Vedatori/PaLampa/Manuals/SupportFiles/IMG_4655.jpeg

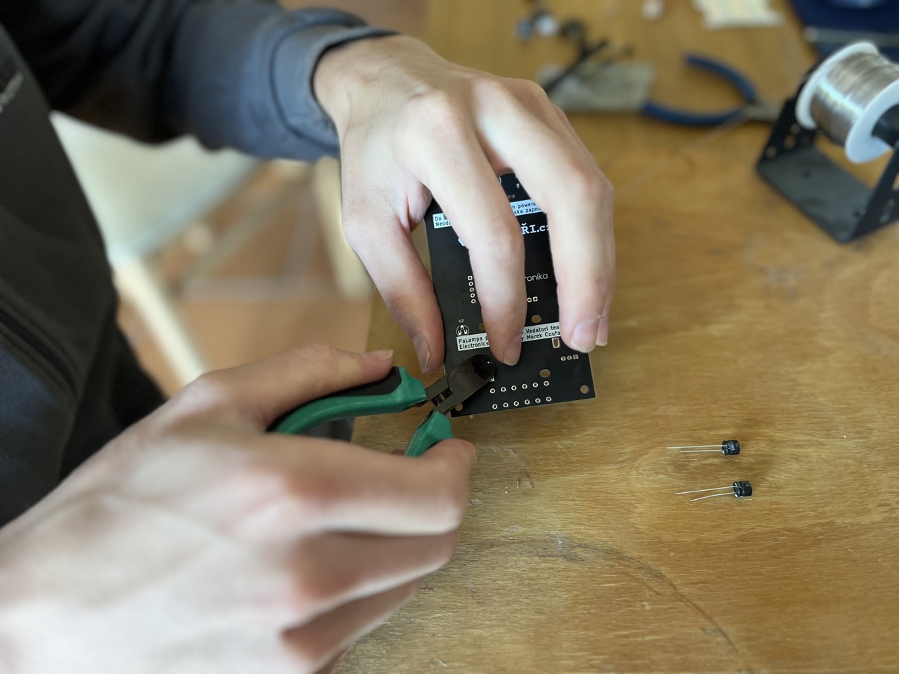
Manuals/SupportFiles/IMG_4655.jpeg
