Vedatori/PaLampa/Manuals/SupportFiles/IMG_4656.jpeg

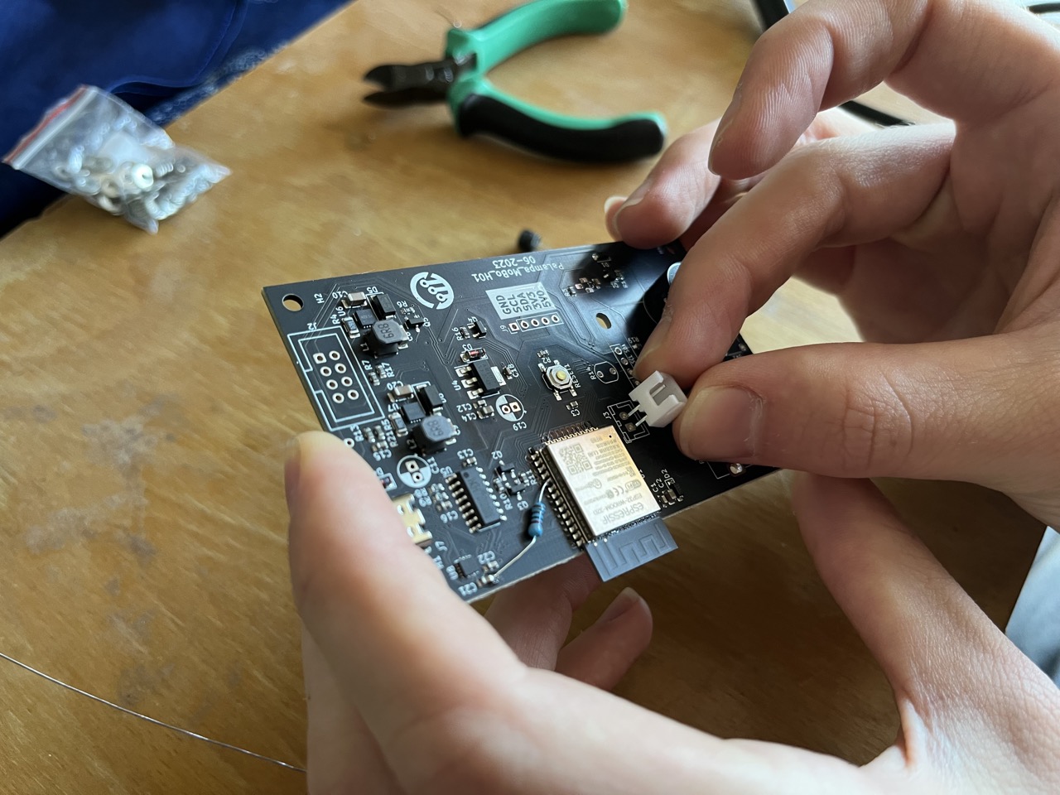
Manuals/SupportFiles/IMG_4656.jpeg
