Vedatori/PaLampa/Manuals/SupportFiles/IMG_4730.jpeg

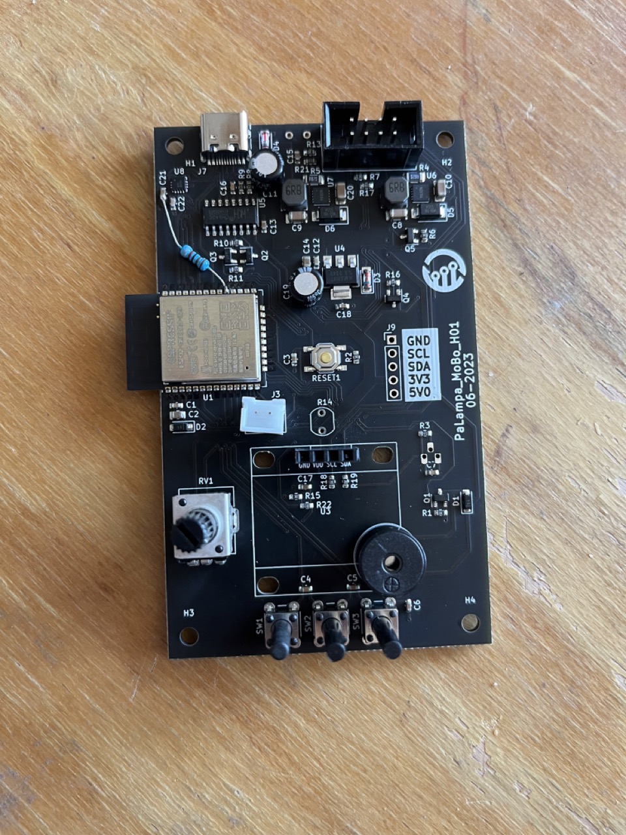
Manuals/SupportFiles/IMG_4730.jpeg
