Vedatori/PaLampa/Manuals/SupportFiles/IMG_5051.jpeg

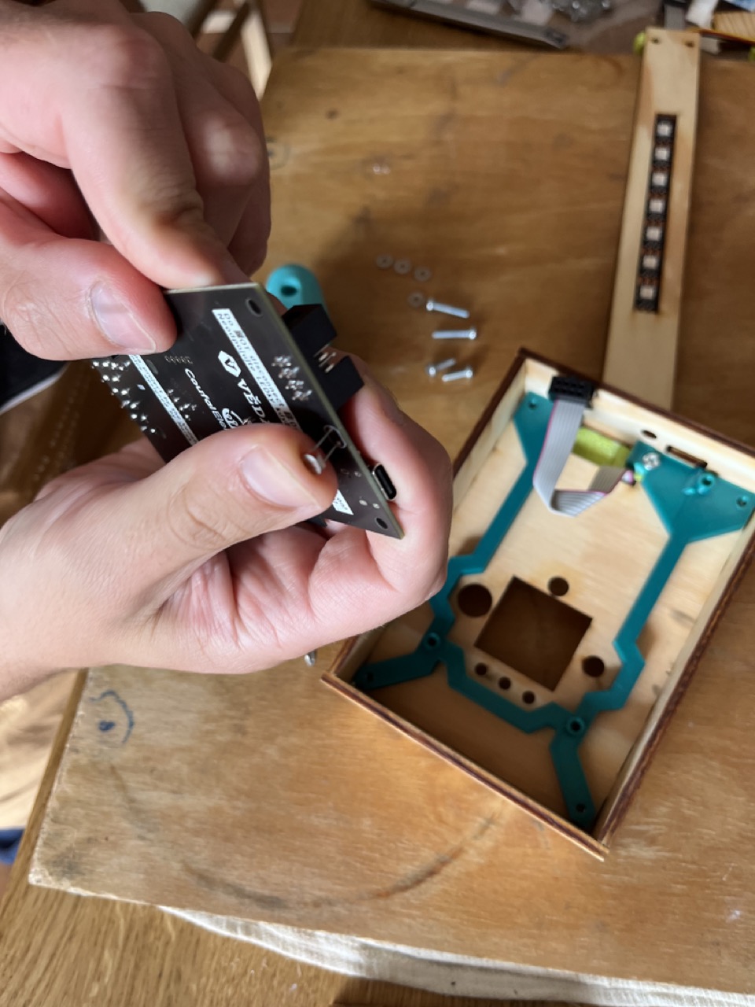
Manuals/SupportFiles/IMG_5051.jpeg
