Vedatori/PaLampa/Manuals/SupportFiles/IMG_5058.jpeg

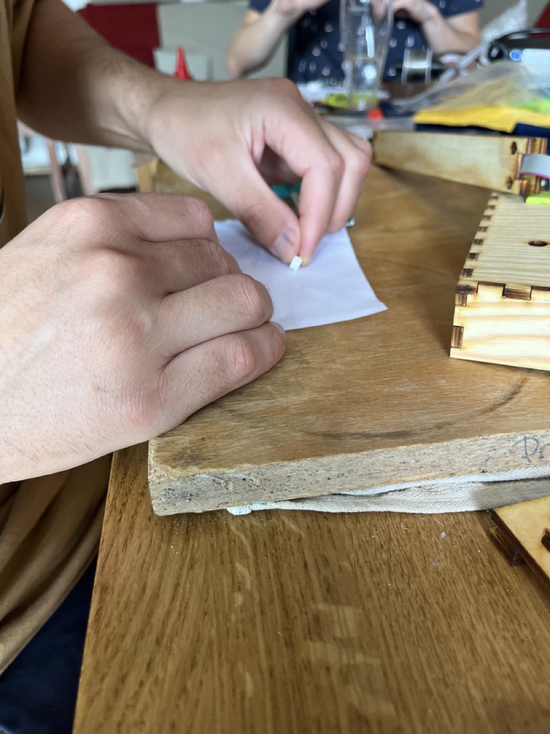
Manuals/SupportFiles/IMG_5058.jpeg
