Vedatori/PaLampa/Manuals/SupportFiles/IMG_5059.jpeg

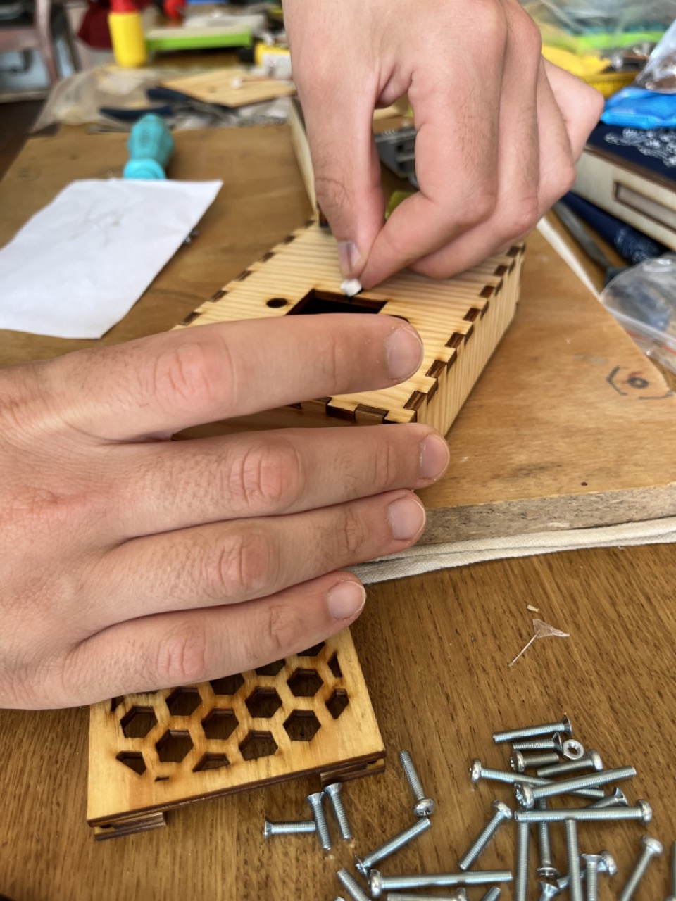
Manuals/SupportFiles/IMG_5059.jpeg
