Vedatori/PaLampa/Manuals/SupportFiles/IMG_5061.jpeg

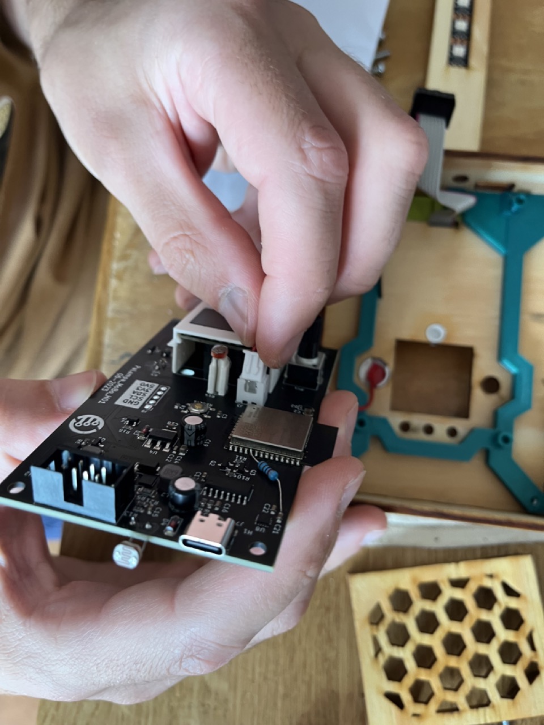
Manuals/SupportFiles/IMG_5061.jpeg
