Vedatori/PaLampa/Manuals/SupportFiles/IMG_5063.jpeg

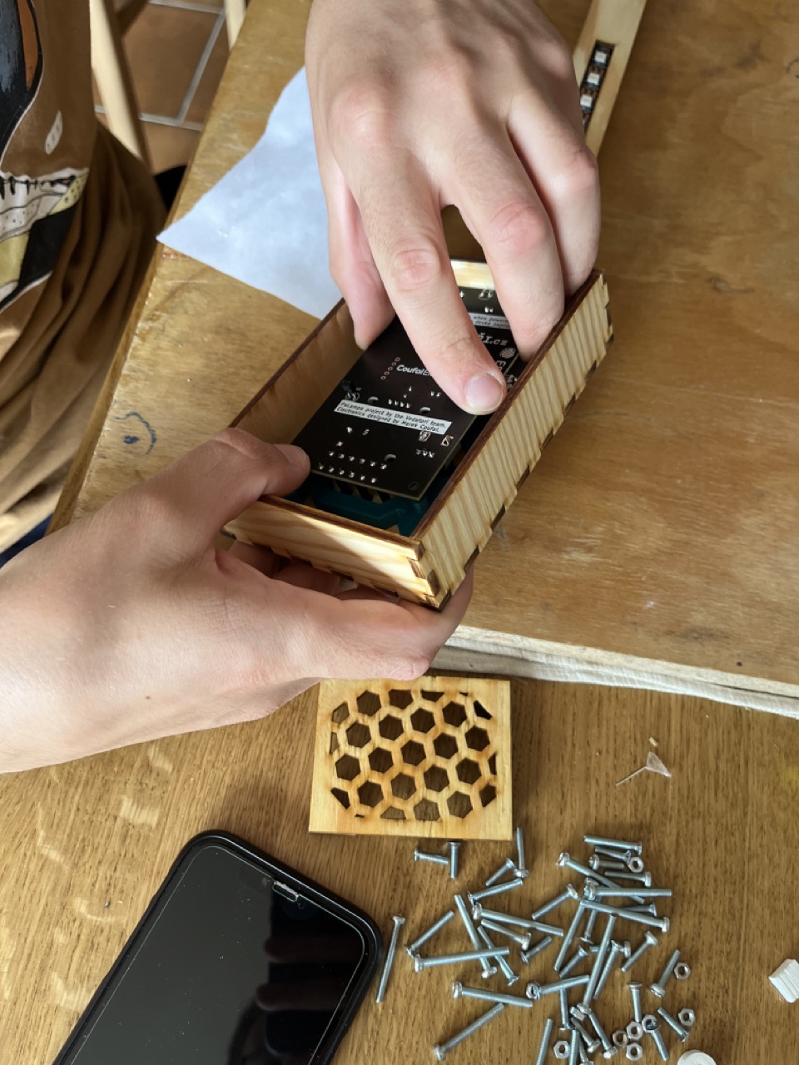
Manuals/SupportFiles/IMG_5063.jpeg
