Vedatori/PaLampa/Manuals/SupportFiles/IMG_5064.jpeg

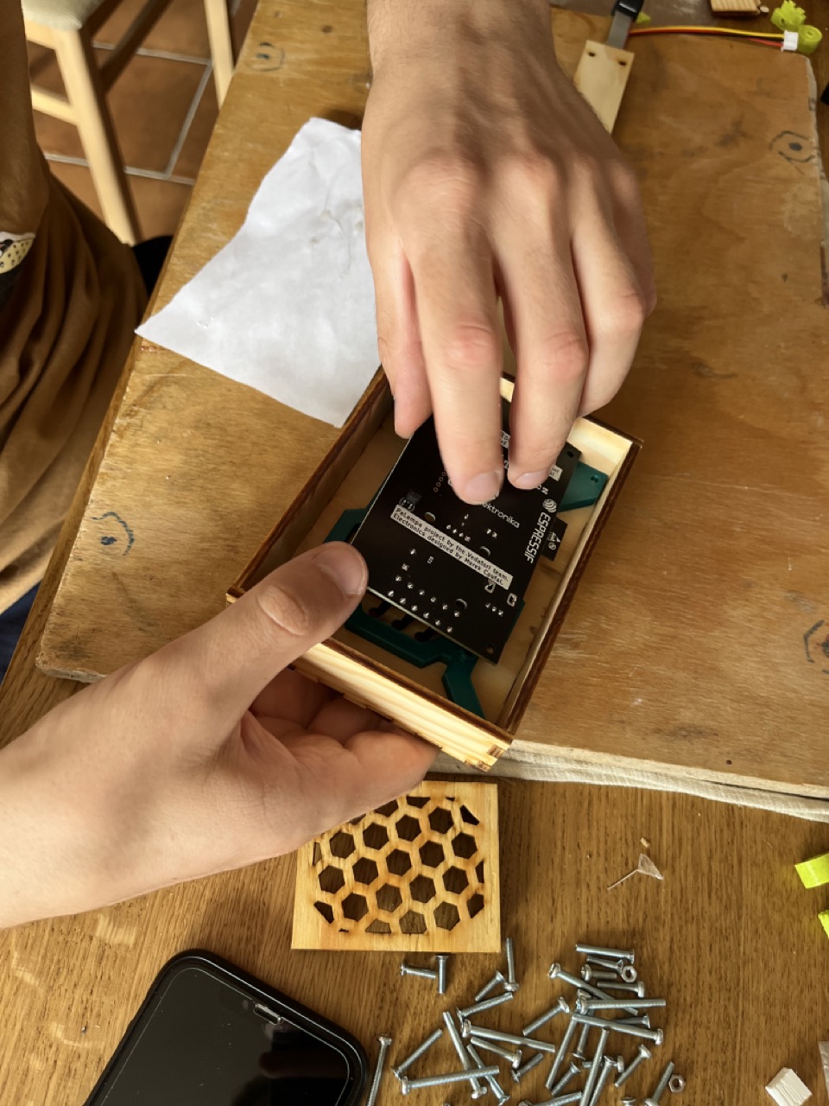
Manuals/SupportFiles/IMG_5064.jpeg
