Vedatori/PaLampa/Manuals/SupportFiles/IMG_5065.jpeg

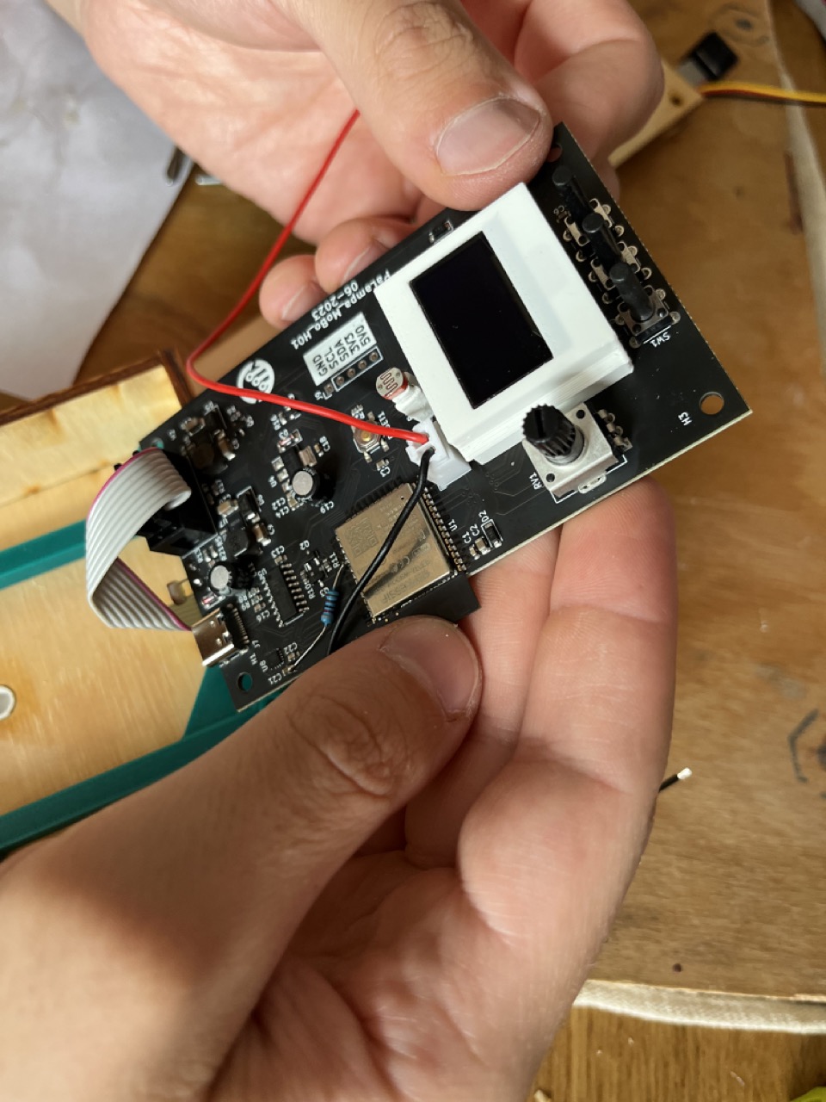
Manuals/SupportFiles/IMG_5065.jpeg
