Vedatori/PaLampa/Manuals/SupportFiles/IMG_5066.jpeg

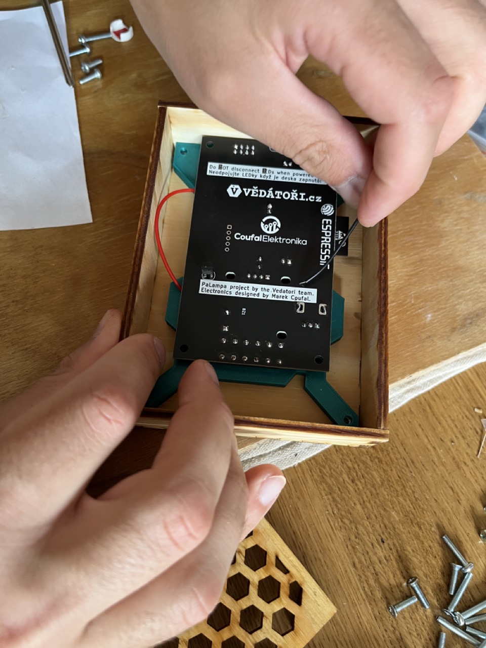
Manuals/SupportFiles/IMG_5066.jpeg
