Vedatori/PaLampa/Manuals/SupportFiles/IMG_5067.jpeg

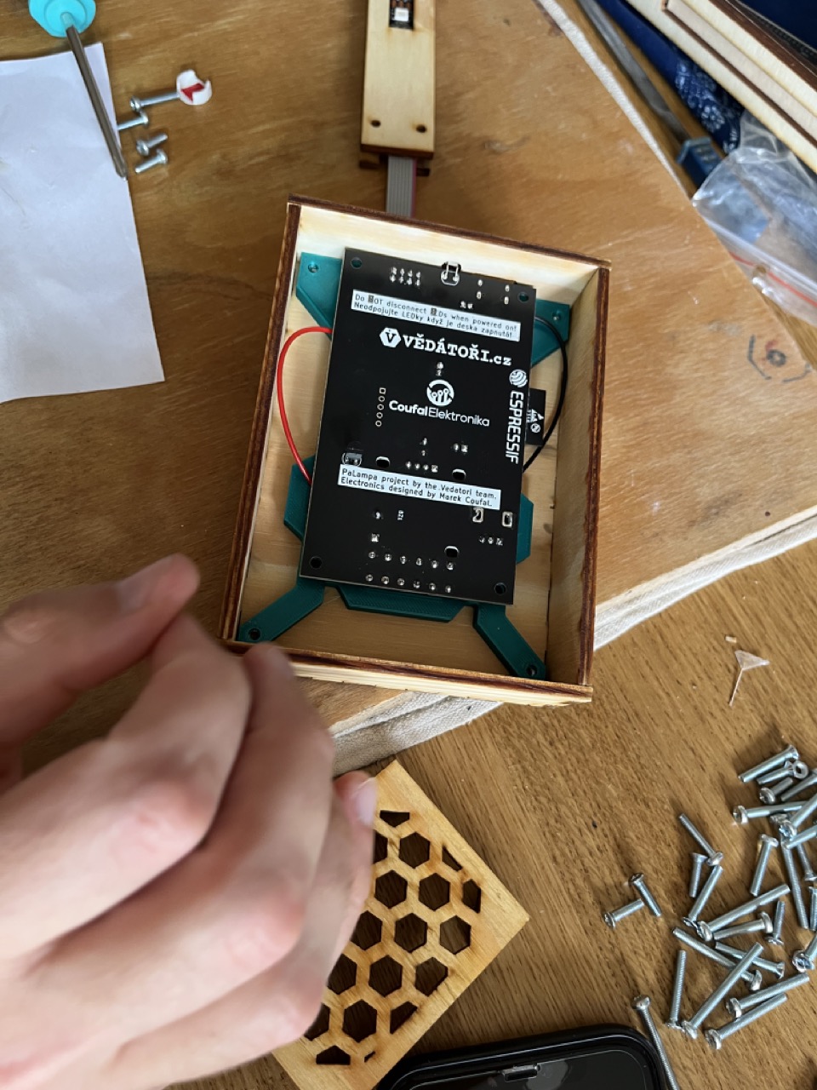
Manuals/SupportFiles/IMG_5067.jpeg
