Vedatori/PaLampa/Manuals/SupportFiles/IMG_5068.jpeg

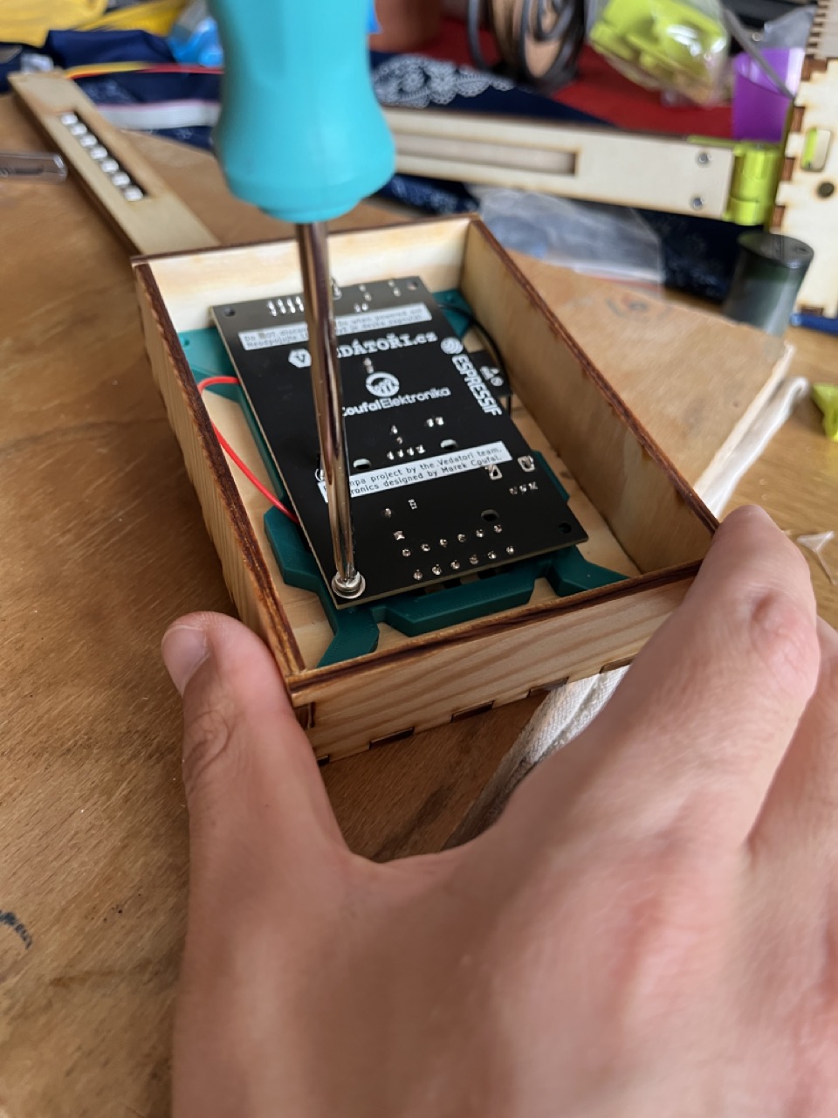
Manuals/SupportFiles/IMG_5068.jpeg
