Vedatori/PaLampa/Manuals/SupportFiles/IMG_5069.jpeg

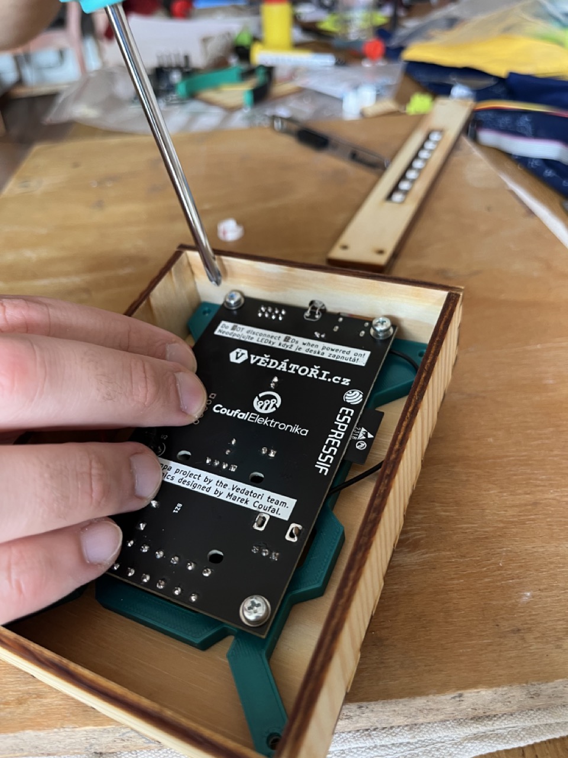
Manuals/SupportFiles/IMG_5069.jpeg
