Vedatori/PaLampa/Manuals/SupportFiles/IMG_5071.jpeg

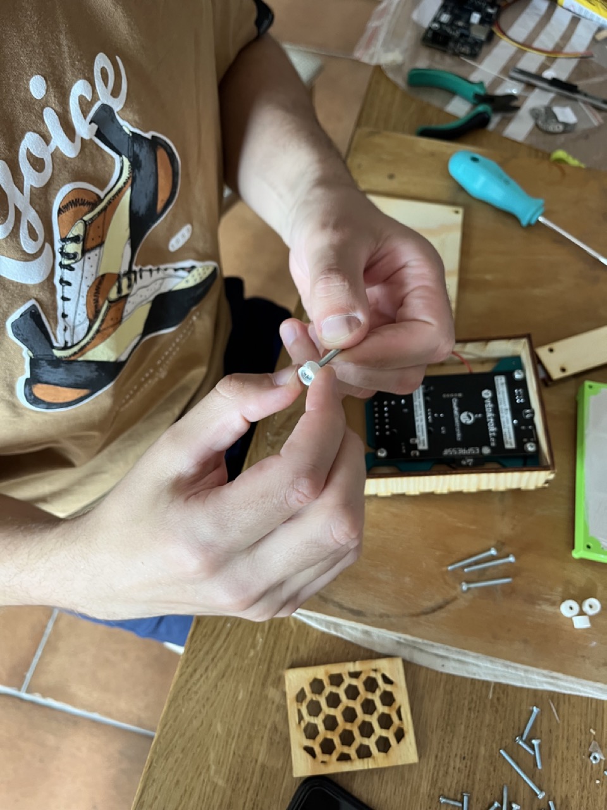
Manuals/SupportFiles/IMG_5071.jpeg
