Vedatori/PaLampa/Manuals/SupportFiles/IMG_5073.jpeg

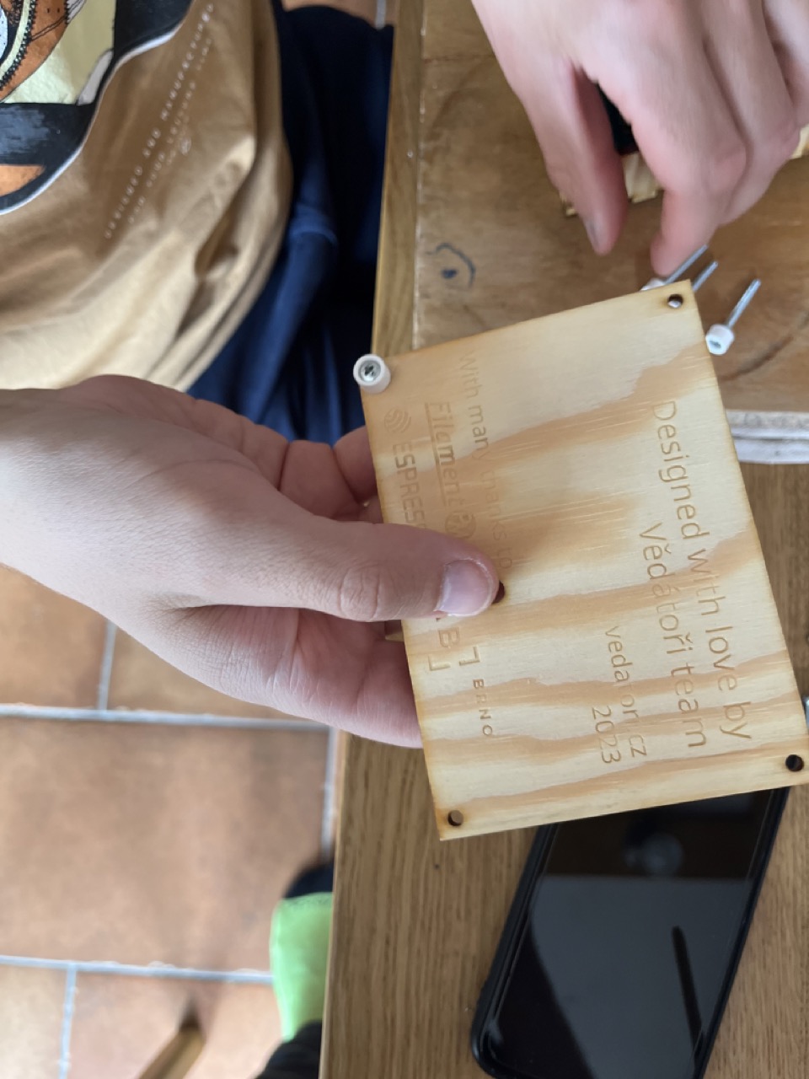
Manuals/SupportFiles/IMG_5073.jpeg
