Vedatori/PaLampa/Manuals/SupportFiles/IMG_5074.jpeg

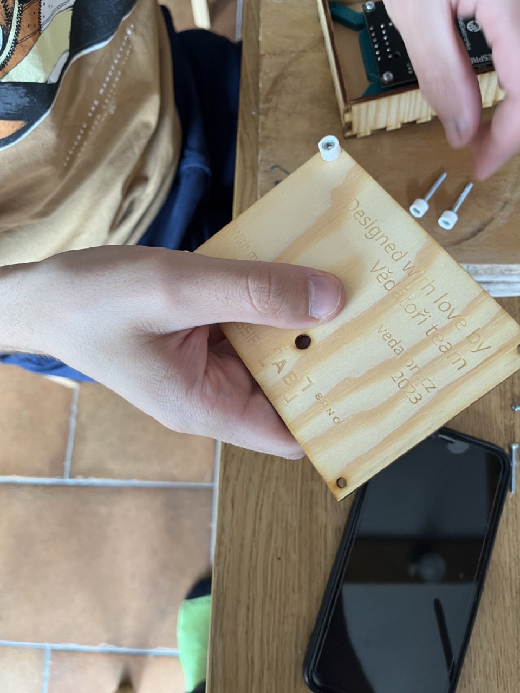
Manuals/SupportFiles/IMG_5074.jpeg
