Vedatori/PaLampa/Manuals/SupportFiles/IMG_5075.jpeg

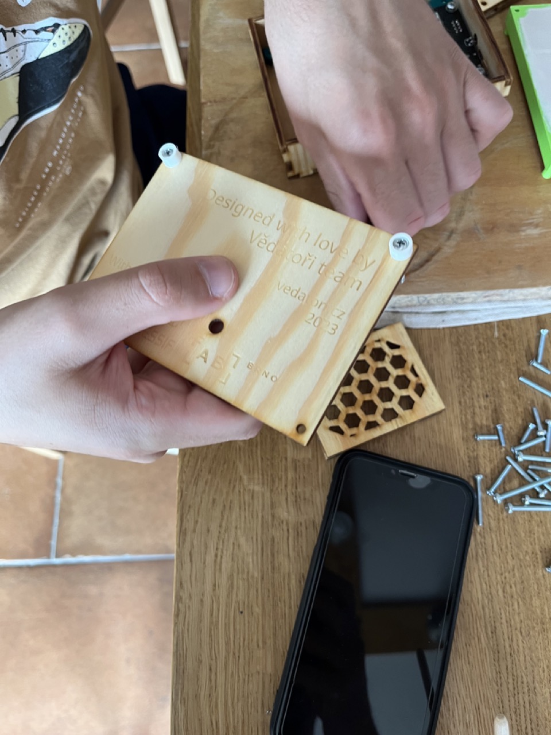
Manuals/SupportFiles/IMG_5075.jpeg
