Vedatori/PaLampa/Manuals/SupportFiles/IMG_5076.jpeg

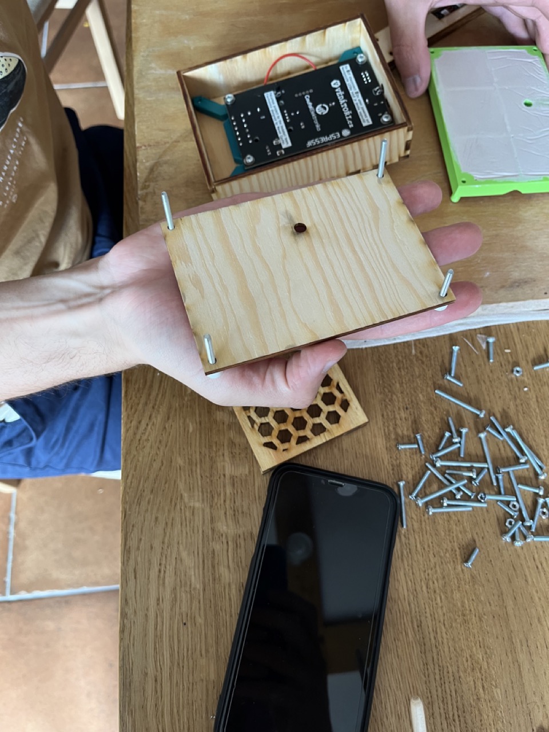
Manuals/SupportFiles/IMG_5076.jpeg
