Vedatori/PaLampa/Manuals/SupportFiles/IMG_5078.jpeg

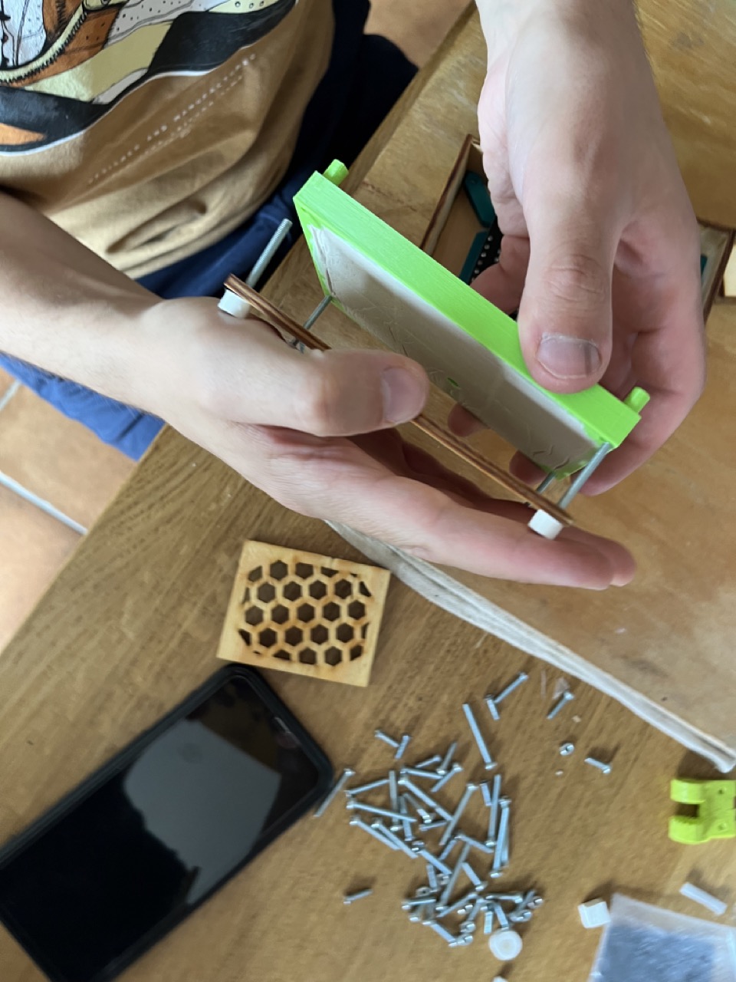
Manuals/SupportFiles/IMG_5078.jpeg
