Vedatori/PaLampa/Manuals/SupportFiles/IMG_5079.jpeg

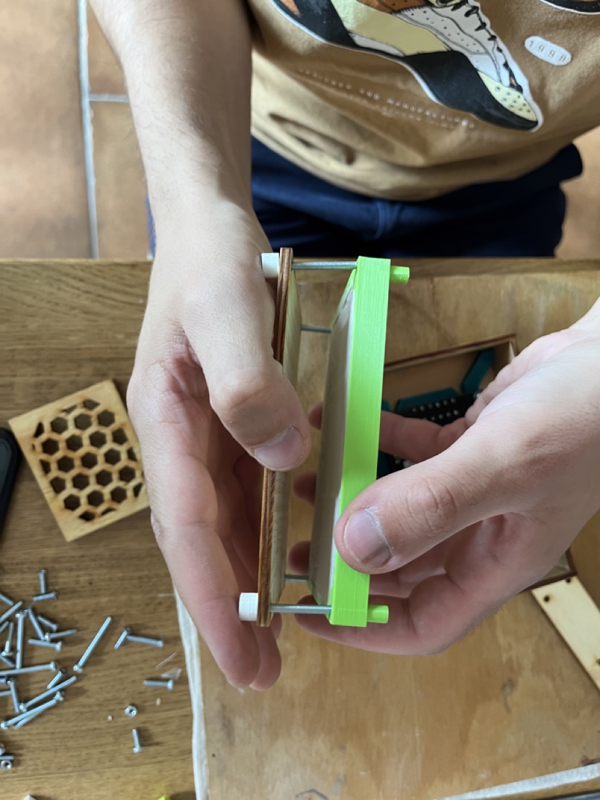
Manuals/SupportFiles/IMG_5079.jpeg
