Vedatori/PaLampa/Manuals/SupportFiles/IMG_5080.jpeg

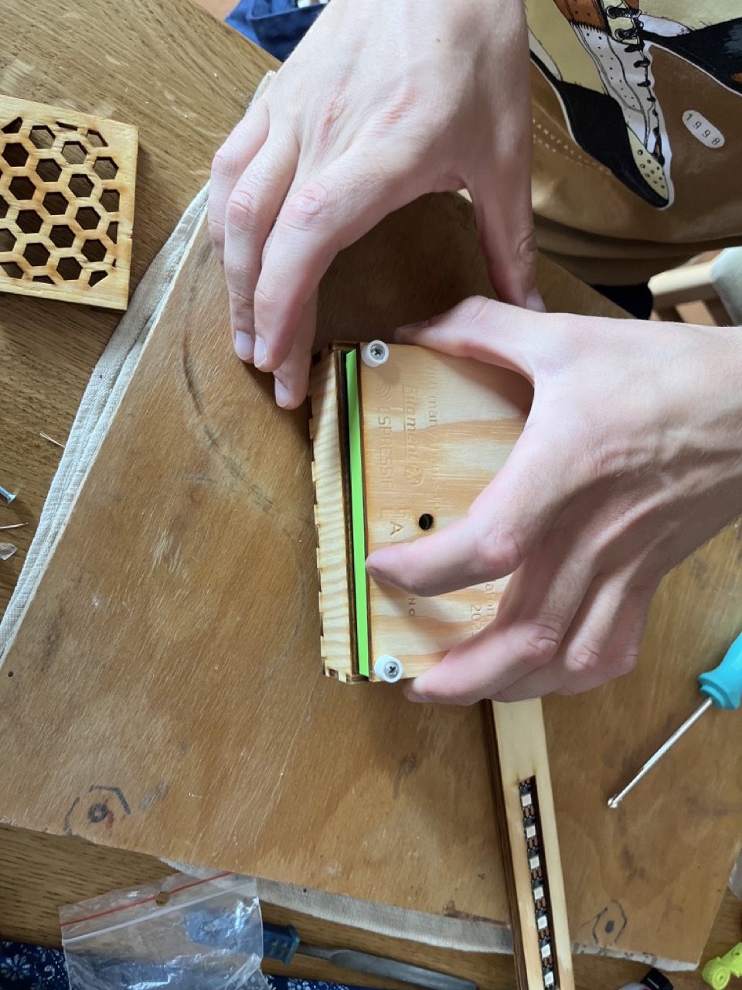
Manuals/SupportFiles/IMG_5080.jpeg
