Vedatori/PaLampa/Manuals/SupportFiles/IMG_5081.jpeg

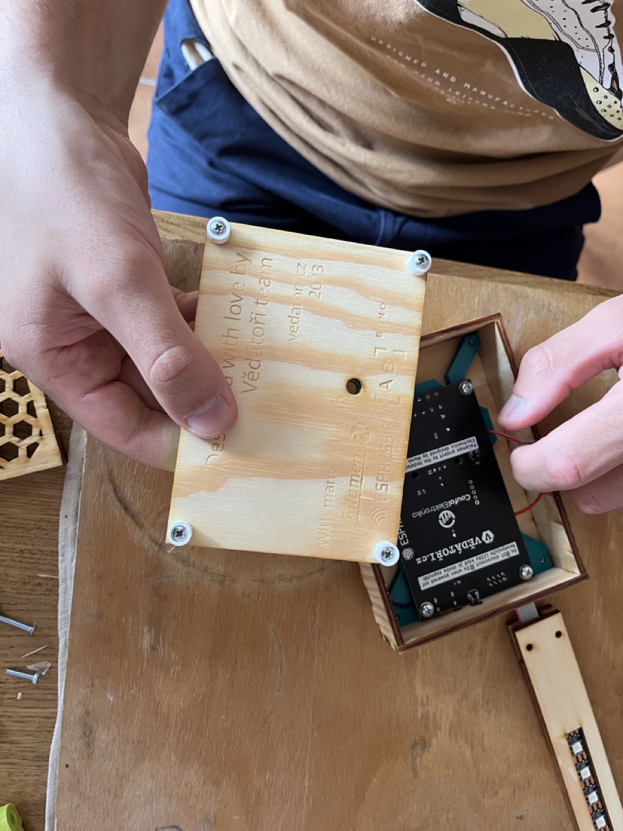
Manuals/SupportFiles/IMG_5081.jpeg
