Vedatori/PaLampa/Manuals/SupportFiles/IMG_5082.jpeg

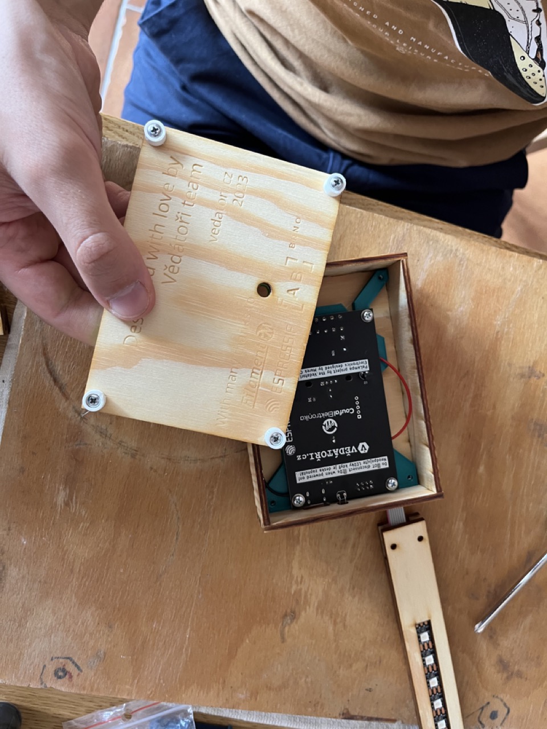
Manuals/SupportFiles/IMG_5082.jpeg
