Vedatori/PaLampa/Manuals/SupportFiles/IMG_5088.jpeg

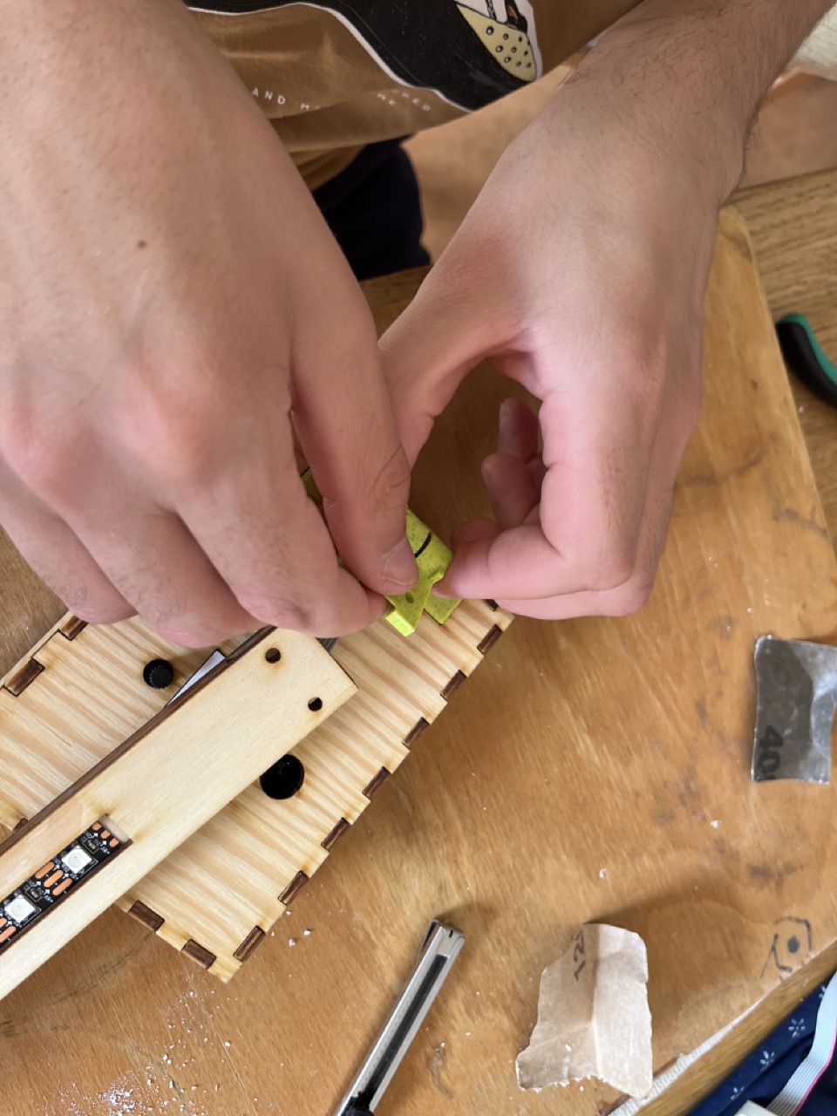
Manuals/SupportFiles/IMG_5088.jpeg
