Vedatori/PaLampa/Manuals/SupportFiles/IMG_5090.jpeg

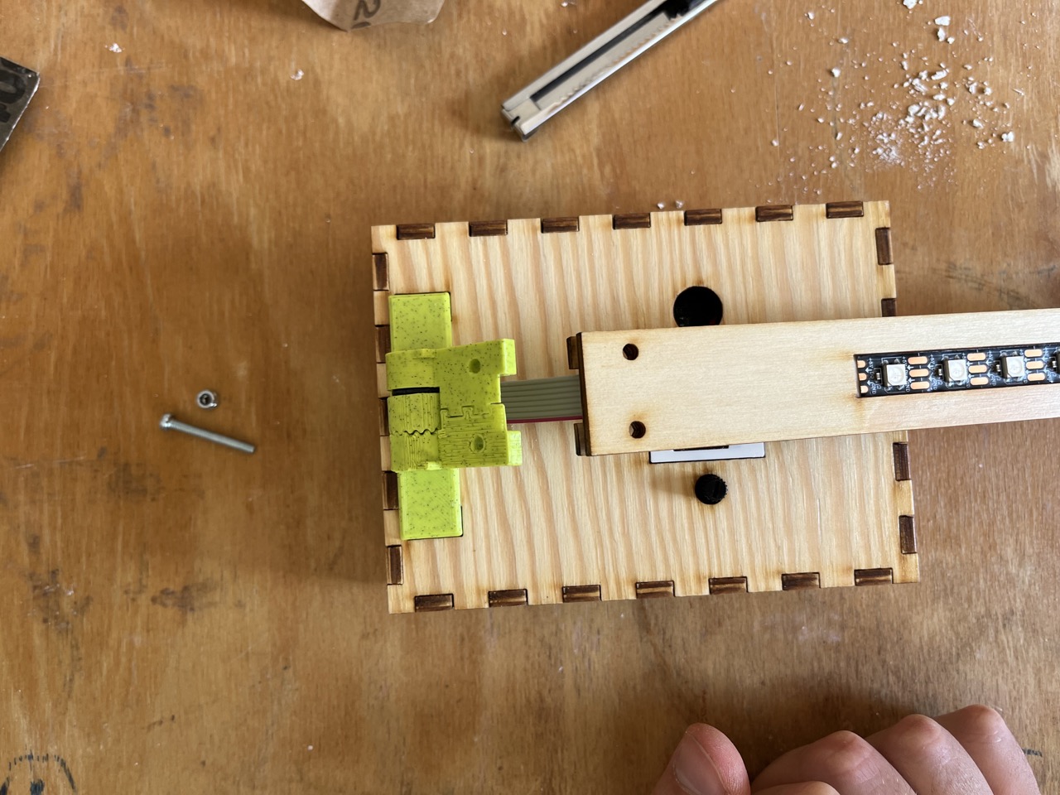
Manuals/SupportFiles/IMG_5090.jpeg
