Vedatori/PaLampa/Manuals/SupportFiles/IMG_5092.jpeg

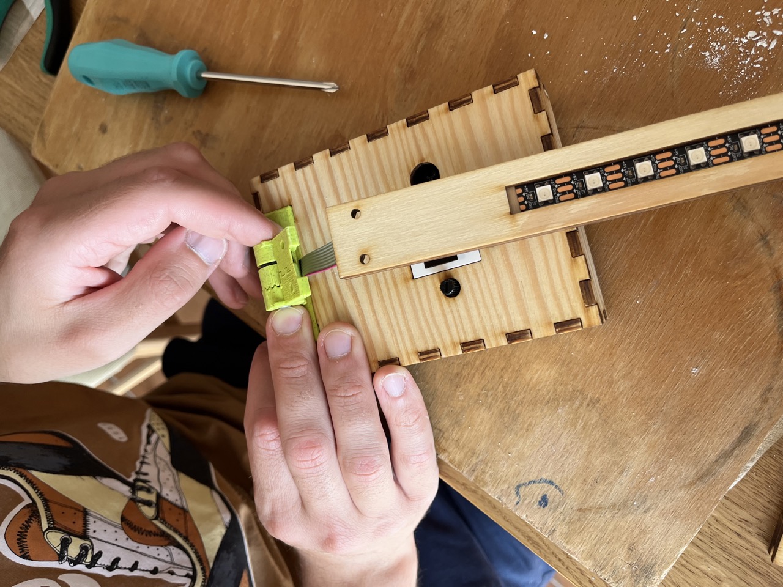
Manuals/SupportFiles/IMG_5092.jpeg
