Vedatori/PaLampa/Manuals/SupportFiles/IMG_5093.jpeg

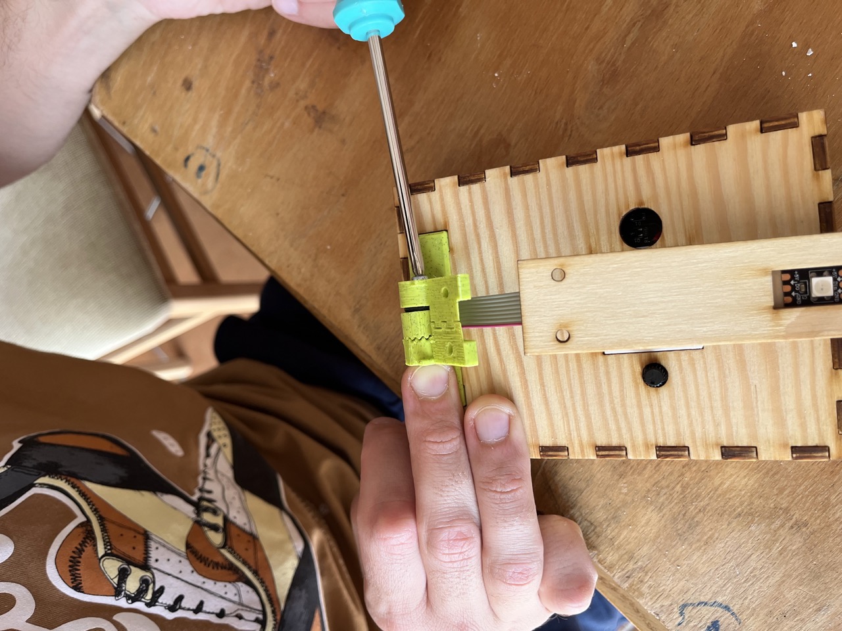
Manuals/SupportFiles/IMG_5093.jpeg
