Vedatori/PaLampa/Manuals/SupportFiles/IMG_5094.jpeg

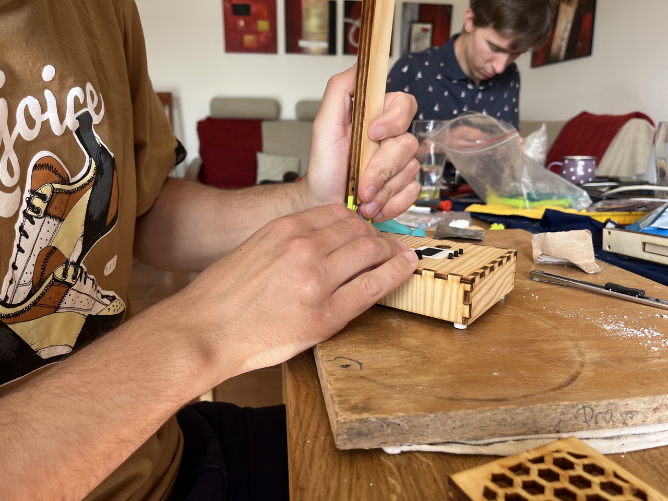
Manuals/SupportFiles/IMG_5094.jpeg
