Vedatori/PaLampa/Manuals/SupportFiles/IMG_5096.jpeg

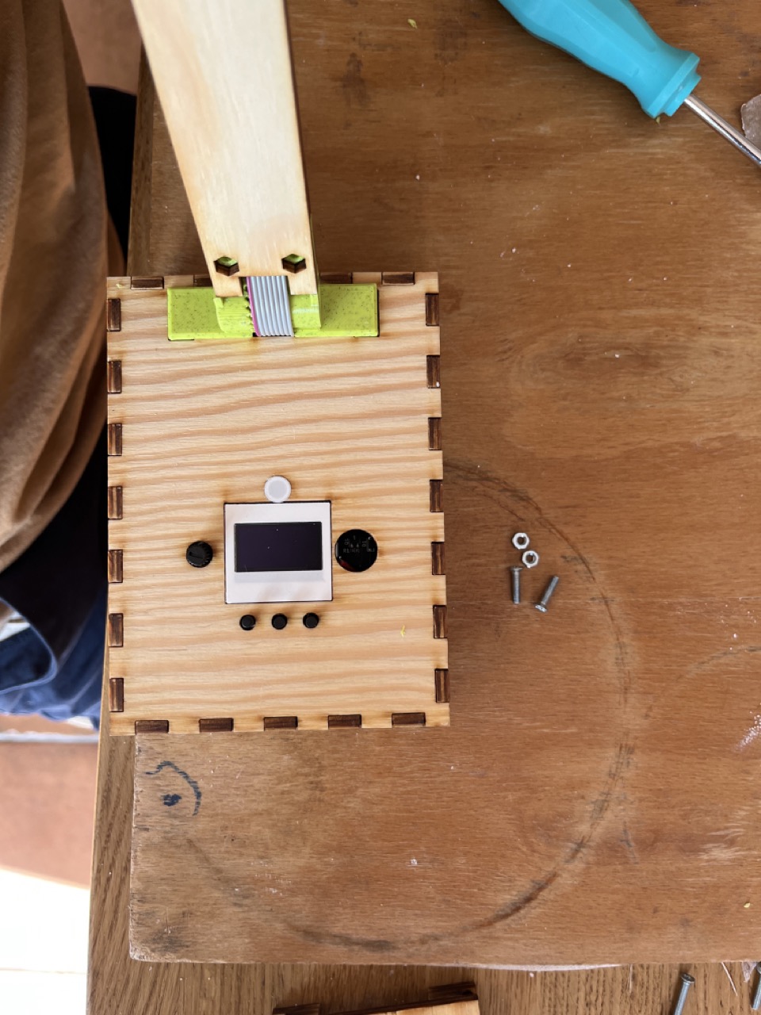
Manuals/SupportFiles/IMG_5096.jpeg
