Vedatori/PaLampa/Manuals/SupportFiles/IMG_5098.jpeg

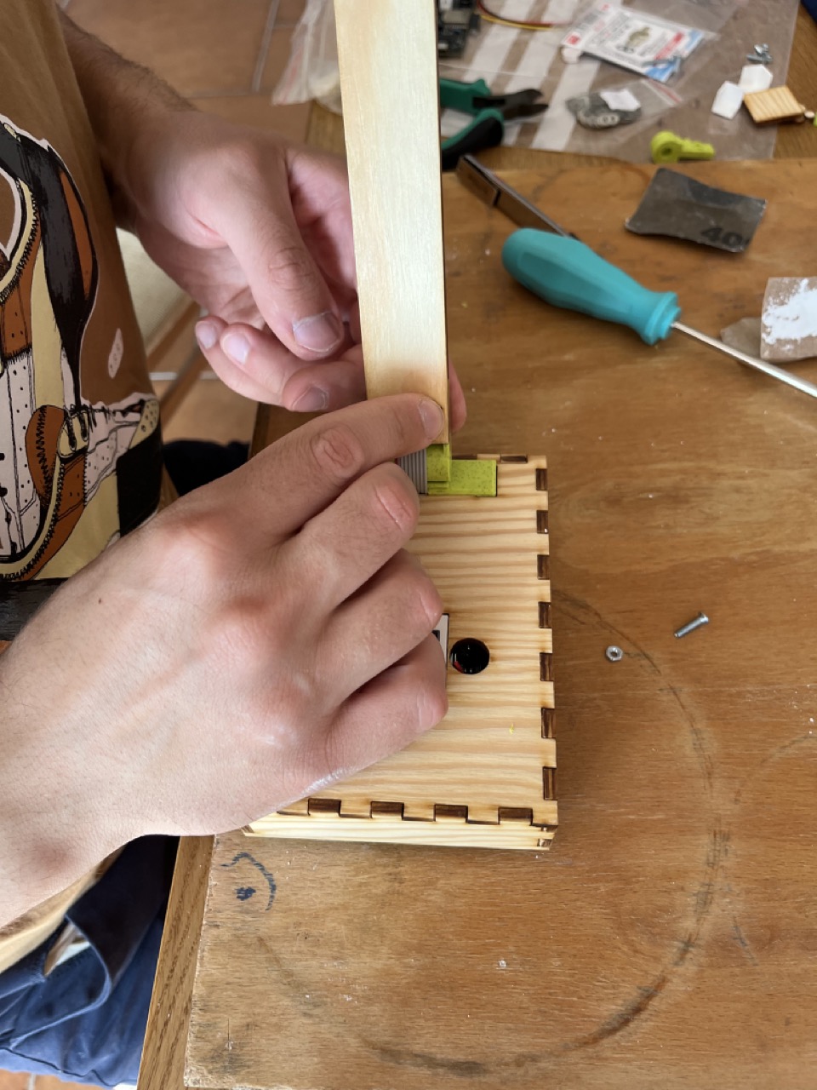
Manuals/SupportFiles/IMG_5098.jpeg
