Vedatori/PaLampa/Manuals/SupportFiles/IMG_5101.jpeg

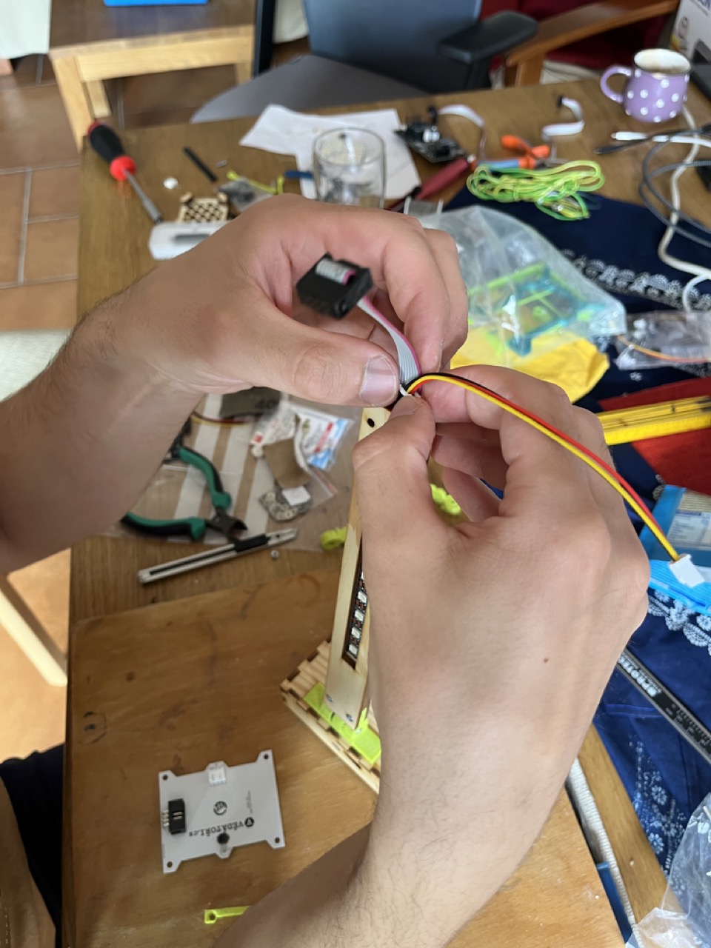
Manuals/SupportFiles/IMG_5101.jpeg
