Vedatori/PaLampa/Manuals/SupportFiles/IMG_5102.jpeg

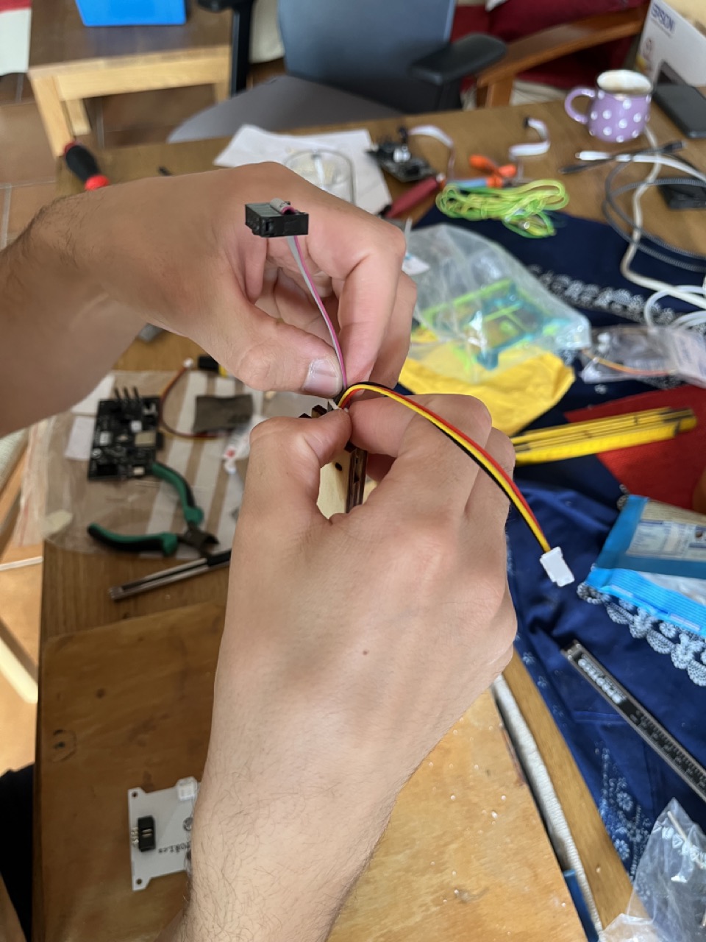
Manuals/SupportFiles/IMG_5102.jpeg
