Vedatori/PaLampa/Manuals/SupportFiles/IMG_5104.jpeg

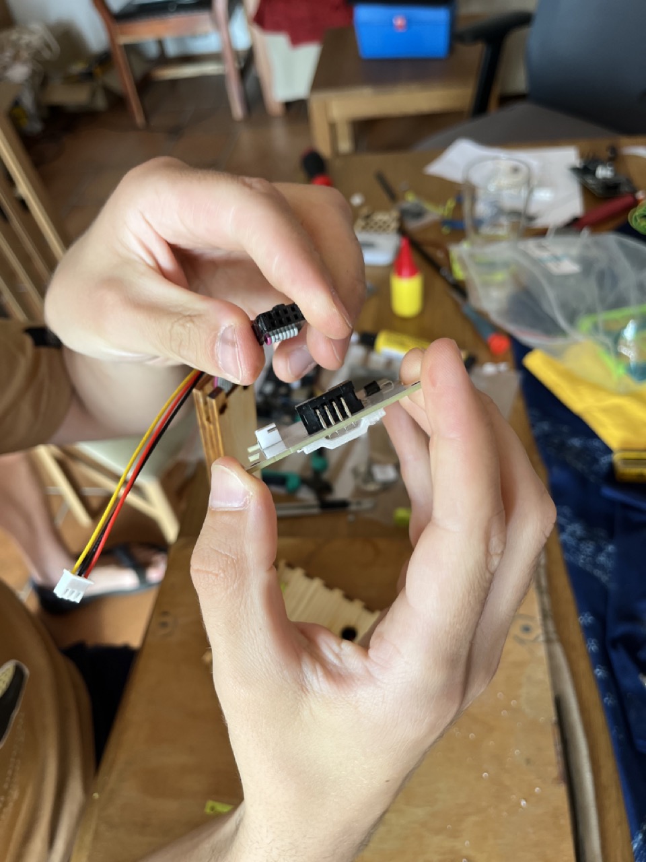
Manuals/SupportFiles/IMG_5104.jpeg
