Vedatori/PaLampa/Manuals/SupportFiles/IMG_5105.jpeg

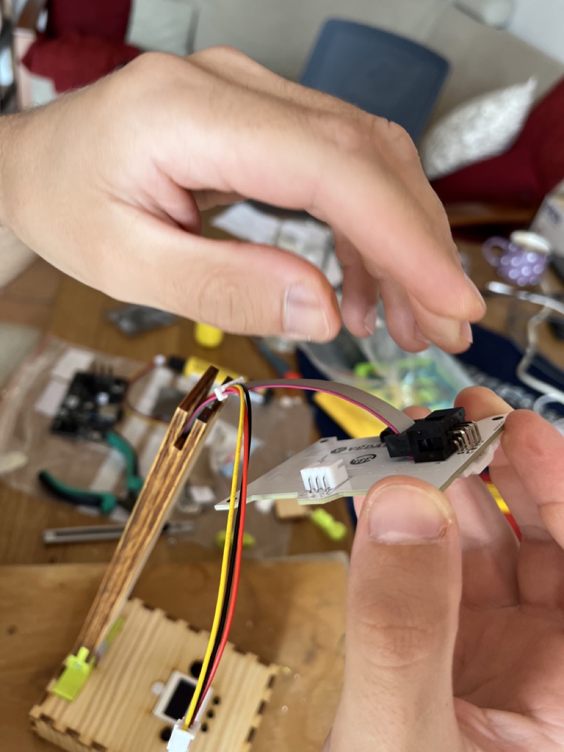
Manuals/SupportFiles/IMG_5105.jpeg
