Vedatori/PaLampa/Manuals/SupportFiles/IMG_5106.jpeg

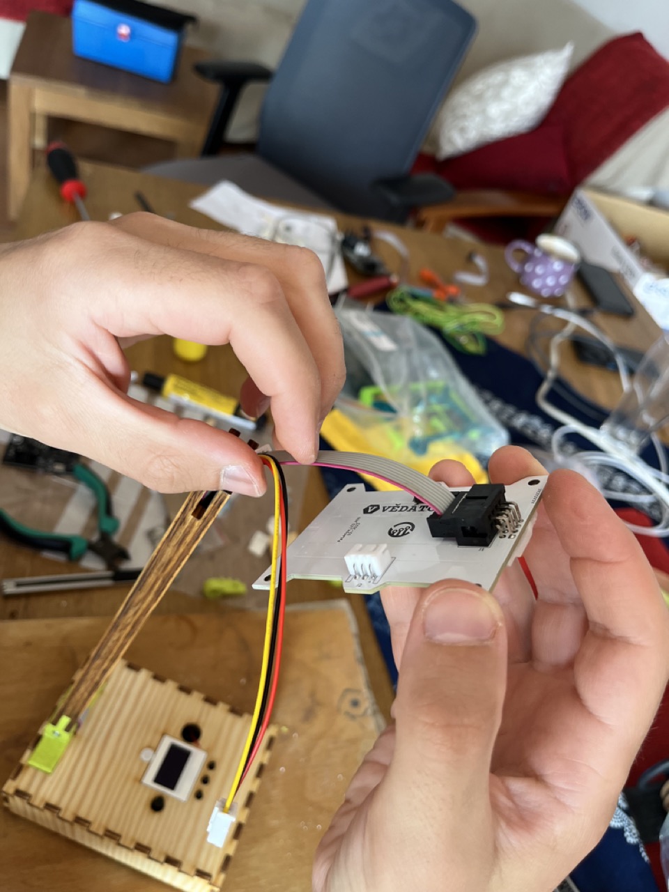
Manuals/SupportFiles/IMG_5106.jpeg
