Vedatori/PaLampa/Manuals/SupportFiles/IMG_5108.jpeg

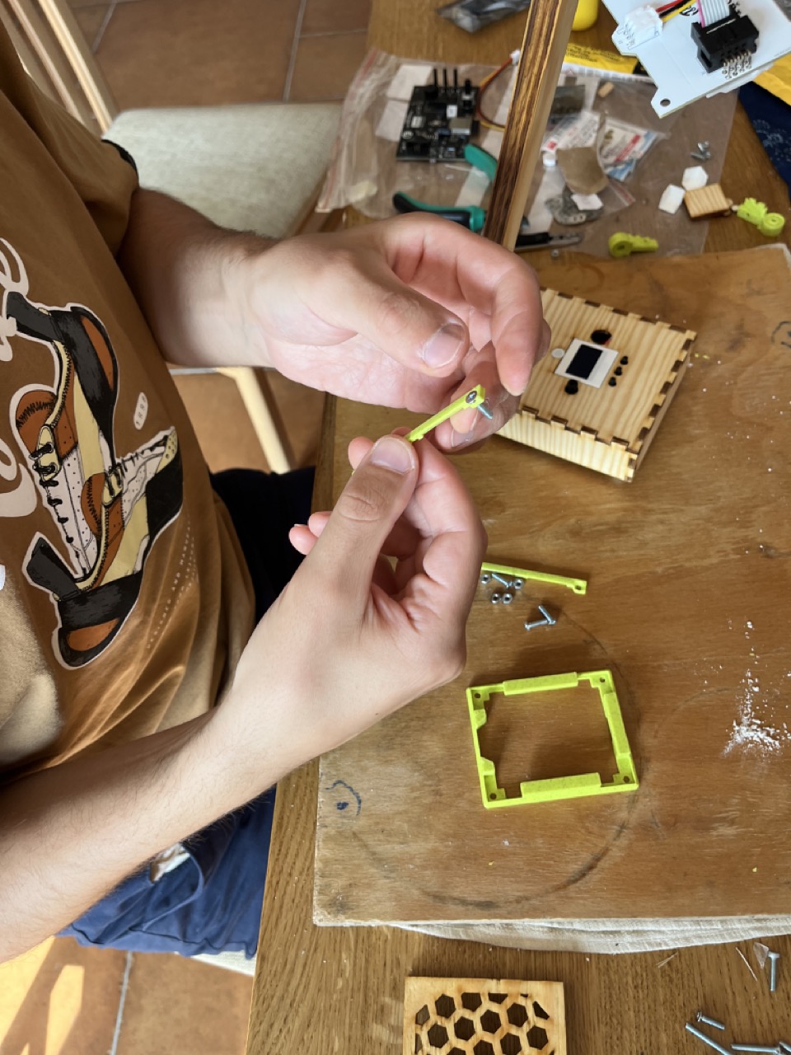
Manuals/SupportFiles/IMG_5108.jpeg
