Vedatori/PaLampa/Manuals/SupportFiles/IMG_5110.jpeg

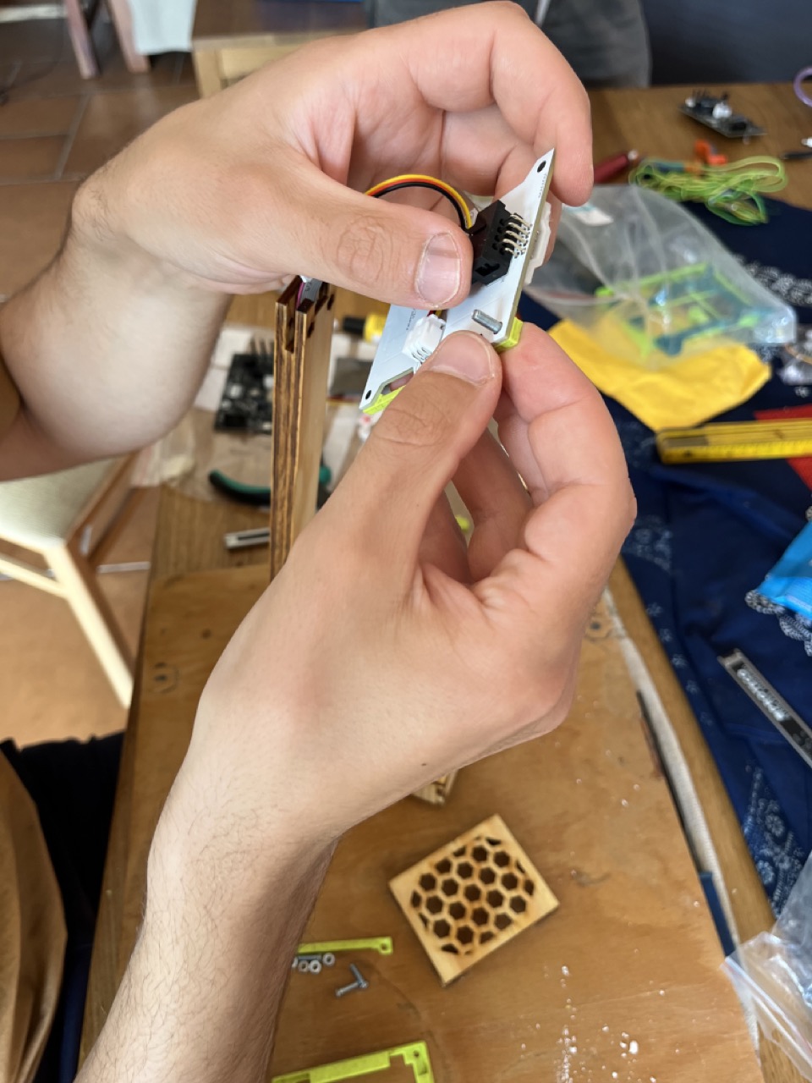
Manuals/SupportFiles/IMG_5110.jpeg
