Vedatori/PaLampa/Manuals/SupportFiles/IMG_5113.jpeg

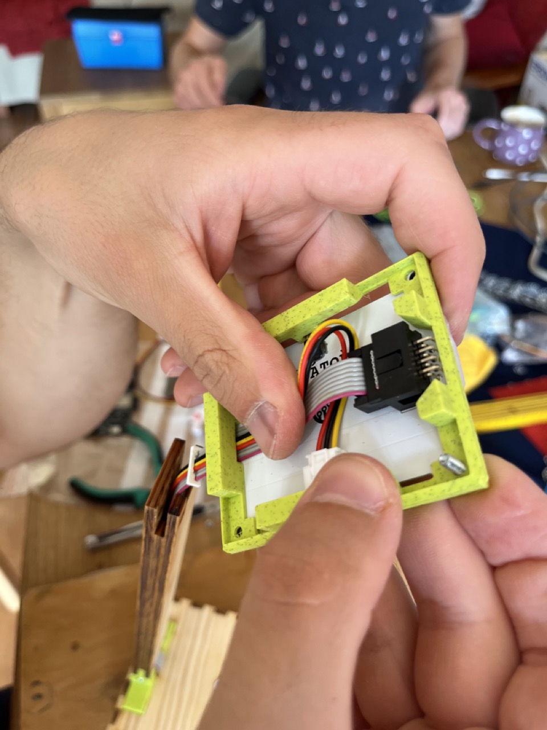
Manuals/SupportFiles/IMG_5113.jpeg
