Vedatori/PaLampa/Manuals/SupportFiles/IMG_5114.jpeg

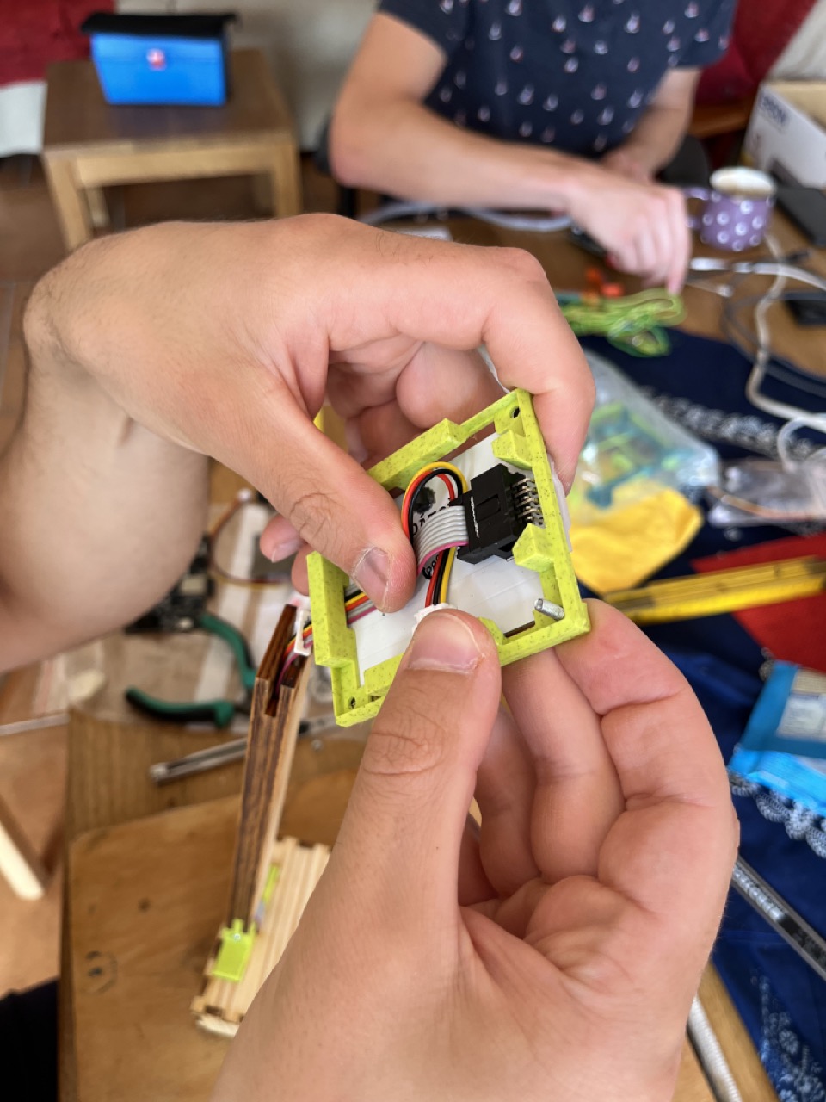
Manuals/SupportFiles/IMG_5114.jpeg
