Vedatori/PaLampa/Manuals/SupportFiles/IMG_5116.jpeg

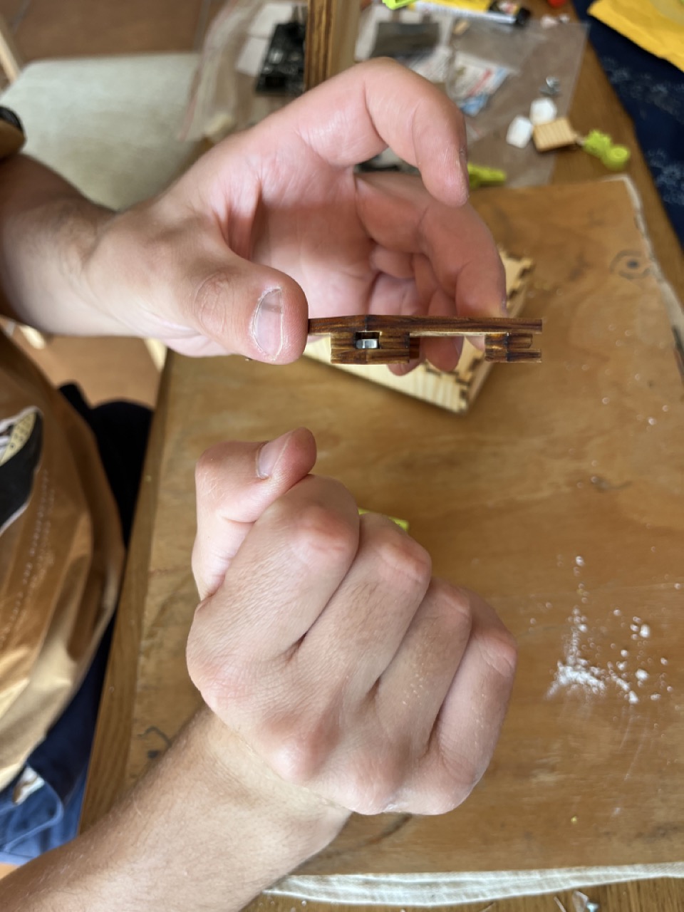
Manuals/SupportFiles/IMG_5116.jpeg
