Vedatori/PaLampa/Manuals/SupportFiles/IMG_5118.jpeg

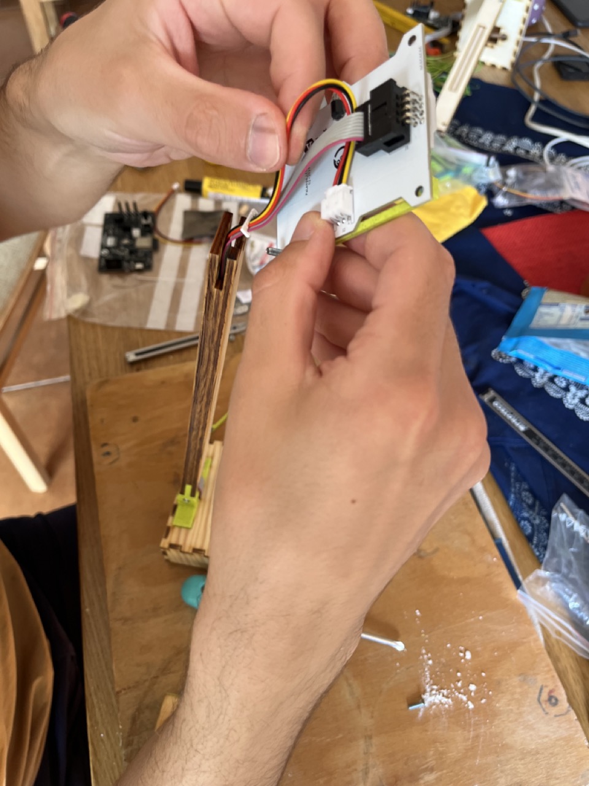
Manuals/SupportFiles/IMG_5118.jpeg
