Vedatori/PaLampa/Manuals/SupportFiles/IMG_5119.jpeg

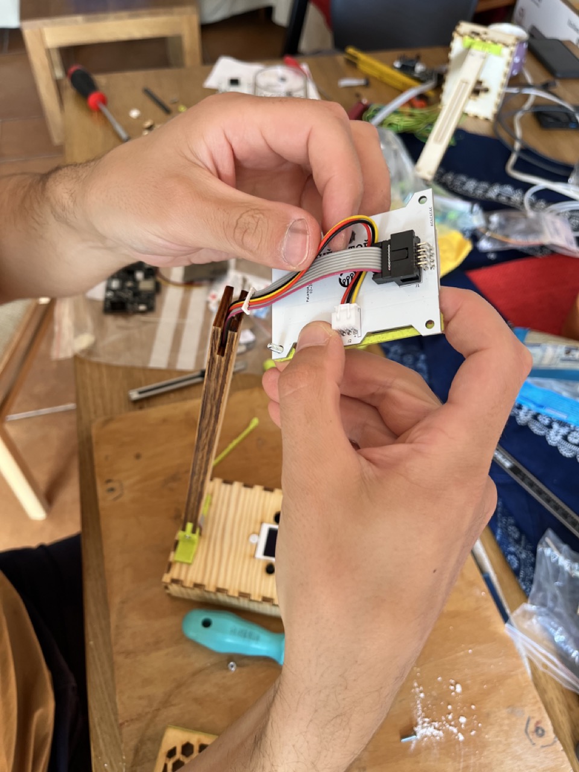
Manuals/SupportFiles/IMG_5119.jpeg
