Vedatori/PaLampa/Manuals/SupportFiles/IMG_5120.jpeg

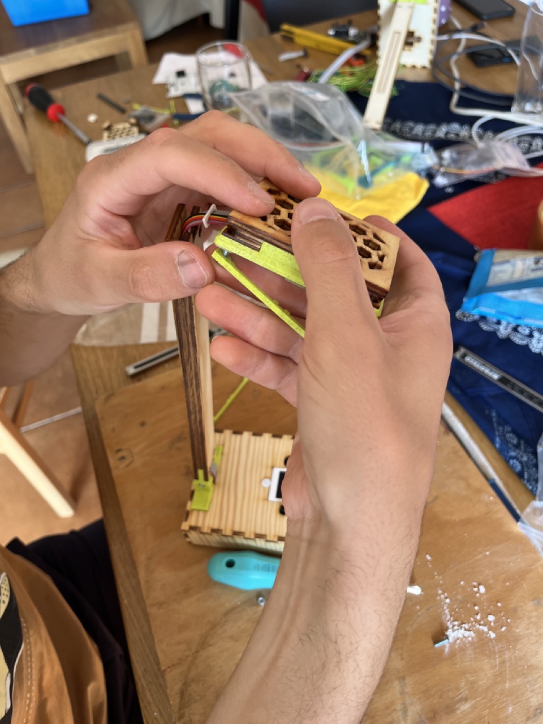
Manuals/SupportFiles/IMG_5120.jpeg
