Vedatori/PaLampa/Manuals/SupportFiles/IMG_5121.jpeg

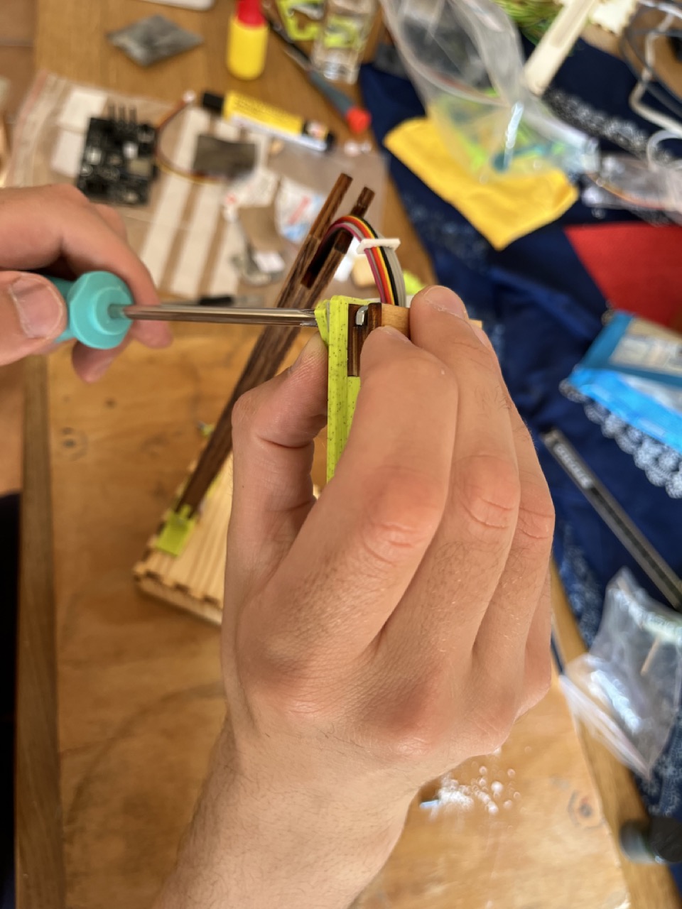
Manuals/SupportFiles/IMG_5121.jpeg
