Vedatori/PaLampa/Manuals/SupportFiles/IMG_5122.jpeg

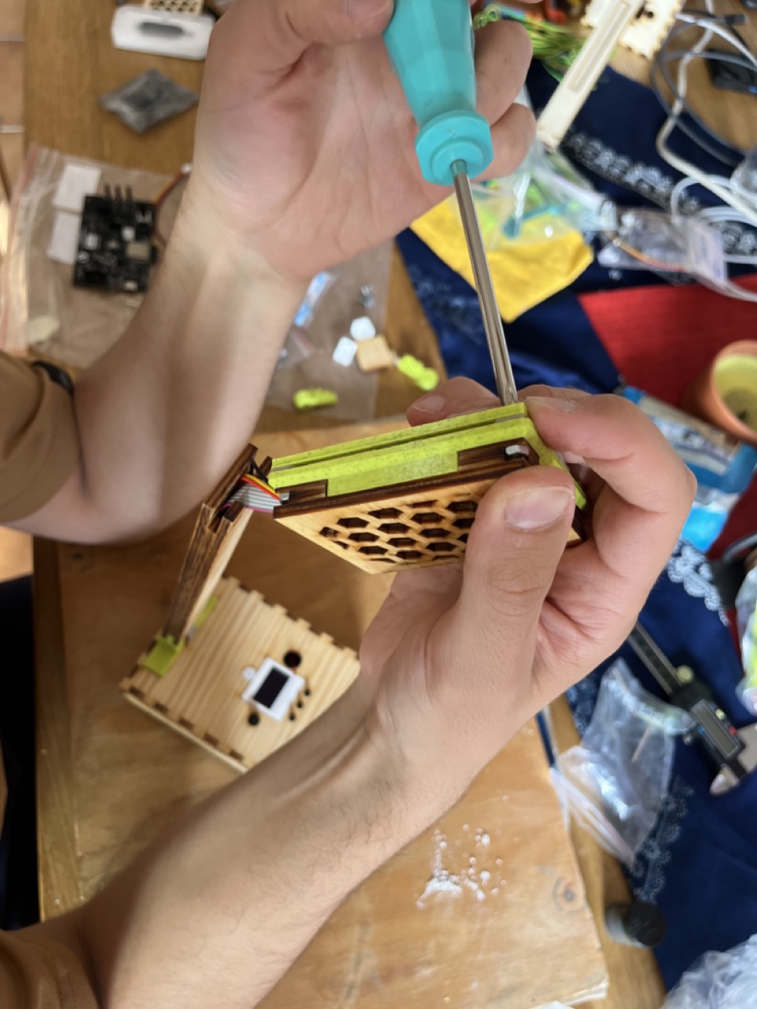
Manuals/SupportFiles/IMG_5122.jpeg
