Vedatori/PaLampa/Manuals/SupportFiles/IMG_5123.jpeg

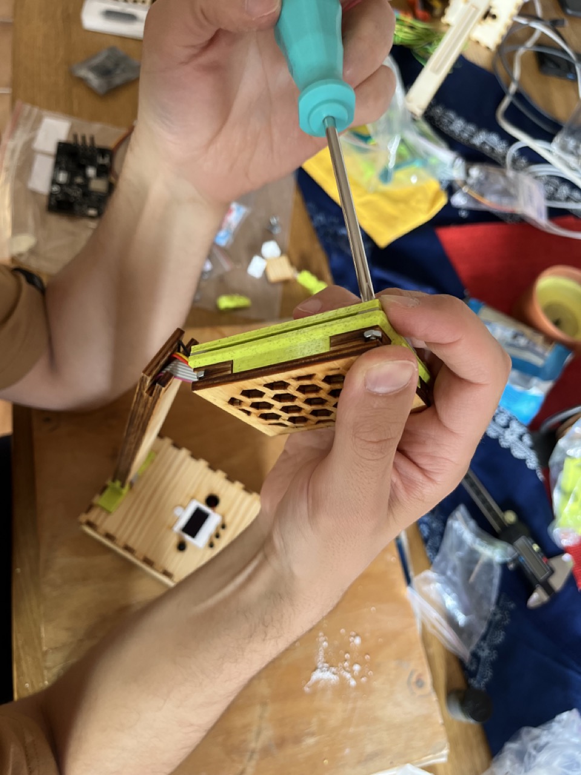
Manuals/SupportFiles/IMG_5123.jpeg
