Vedatori/PaLampa/Manuals/SupportFiles/IMG_5126.jpeg

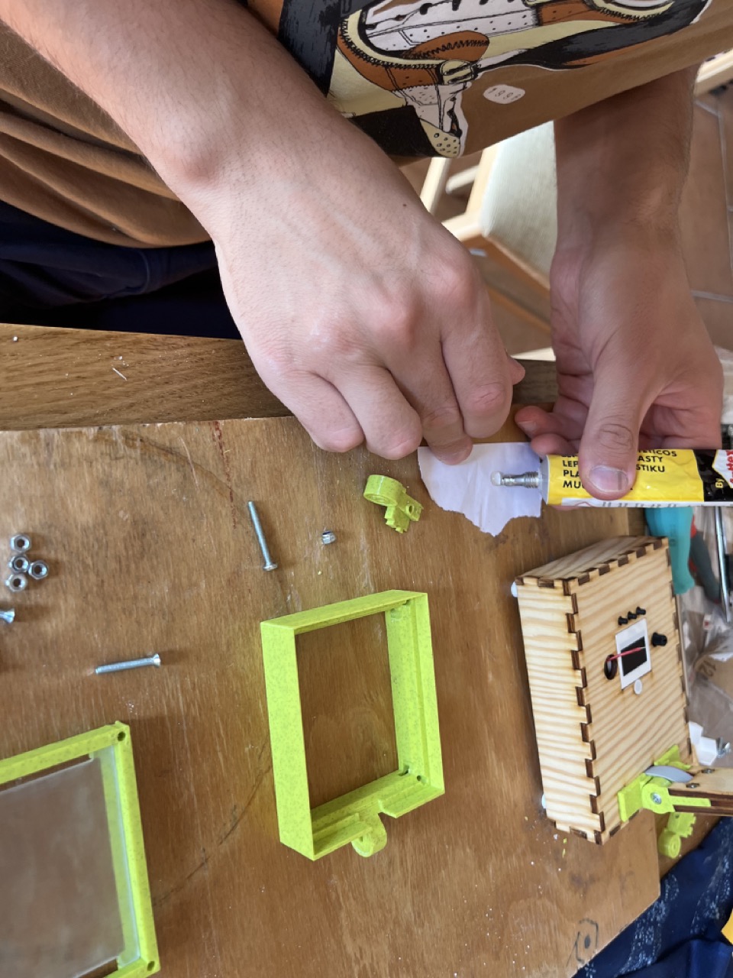
Manuals/SupportFiles/IMG_5126.jpeg
