Vedatori/PaLampa/Manuals/SupportFiles/IMG_5127.jpeg

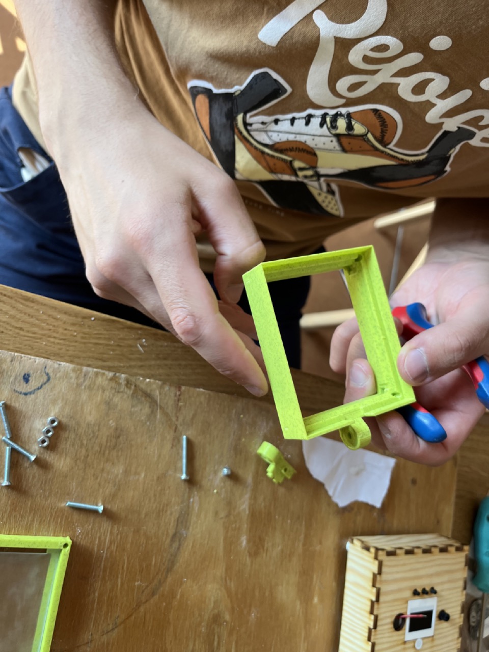
Manuals/SupportFiles/IMG_5127.jpeg
