Vedatori/PaLampa/Manuals/SupportFiles/IMG_5128.jpeg

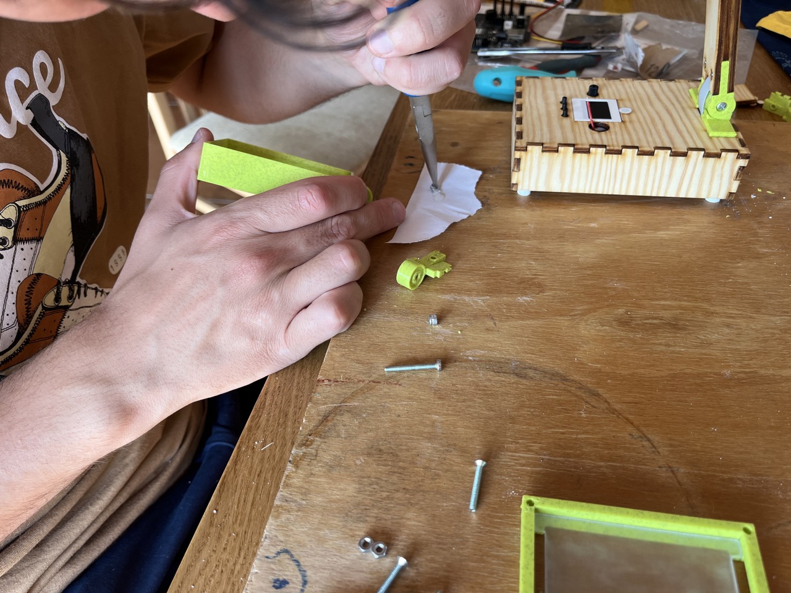
Manuals/SupportFiles/IMG_5128.jpeg
