Vedatori/PaLampa/Manuals/SupportFiles/IMG_5129.jpeg

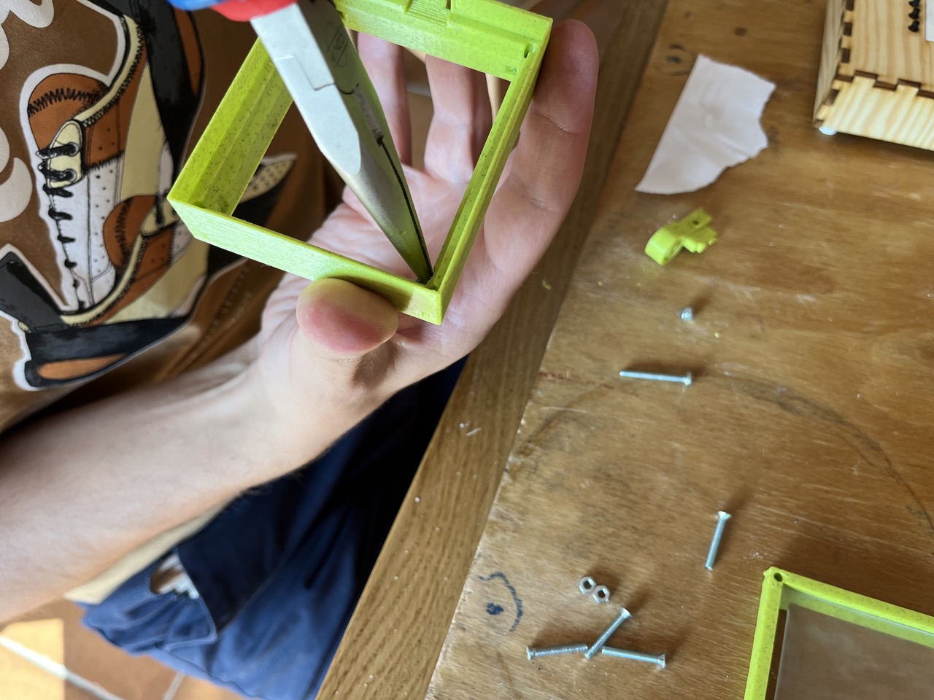
Manuals/SupportFiles/IMG_5129.jpeg
