Vedatori/PaLampa/Manuals/SupportFiles/IMG_5130.jpeg

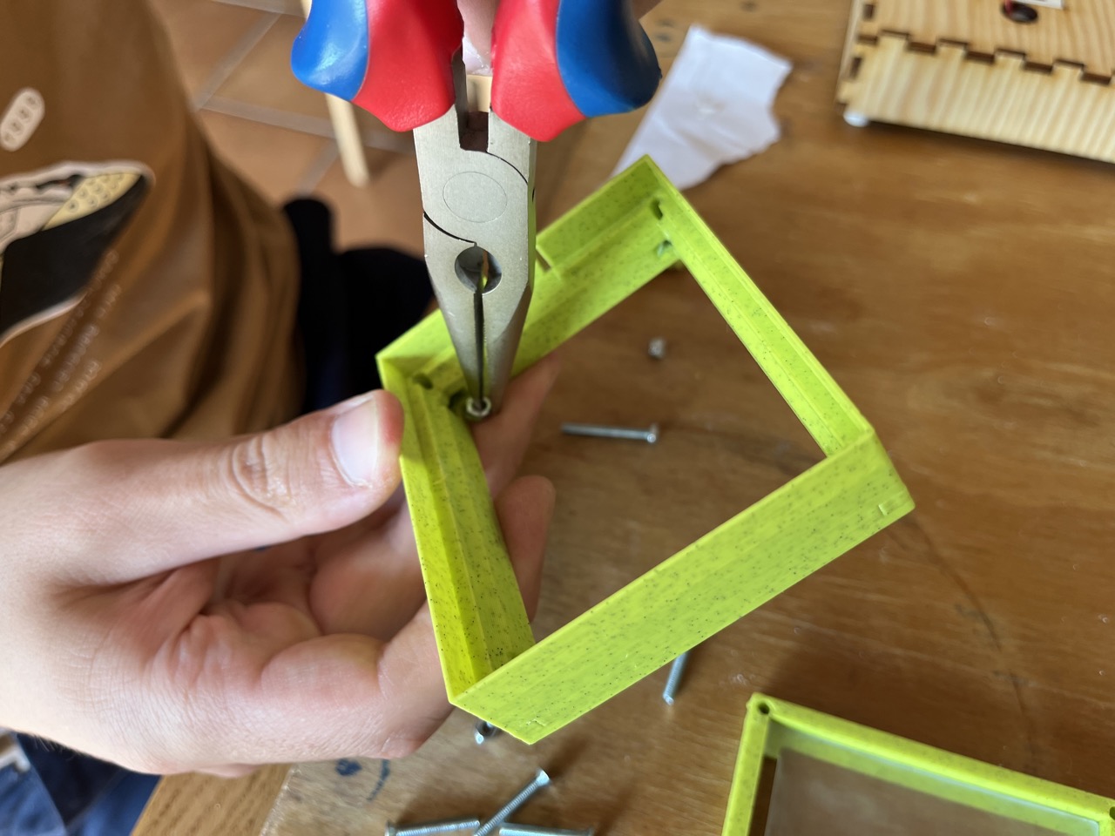
Manuals/SupportFiles/IMG_5130.jpeg
