Vedatori/PaLampa/Manuals/SupportFiles/IMG_5132.jpeg

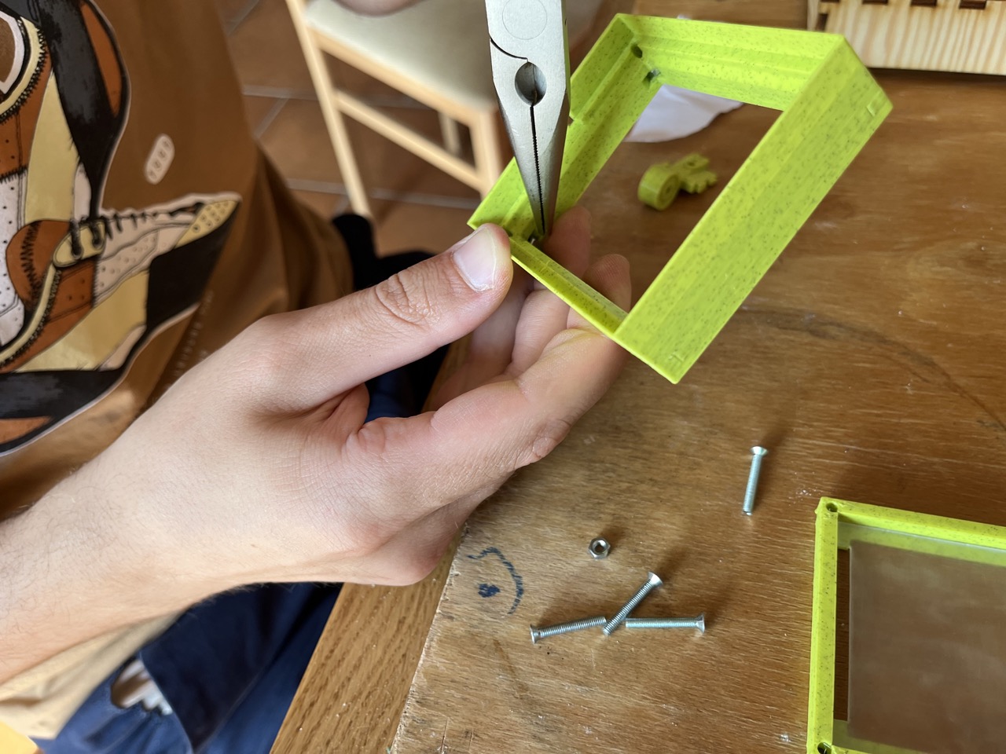
Manuals/SupportFiles/IMG_5132.jpeg
