Vedatori/PaLampa/Manuals/SupportFiles/IMG_5133.jpeg

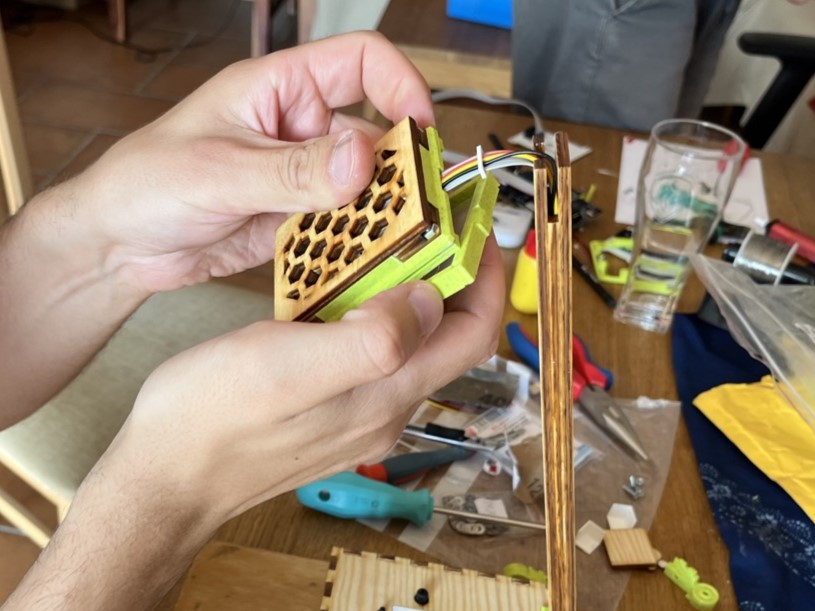
Manuals/SupportFiles/IMG_5133.jpeg
