Vedatori/PaLampa/Manuals/SupportFiles/IMG_5134.jpeg

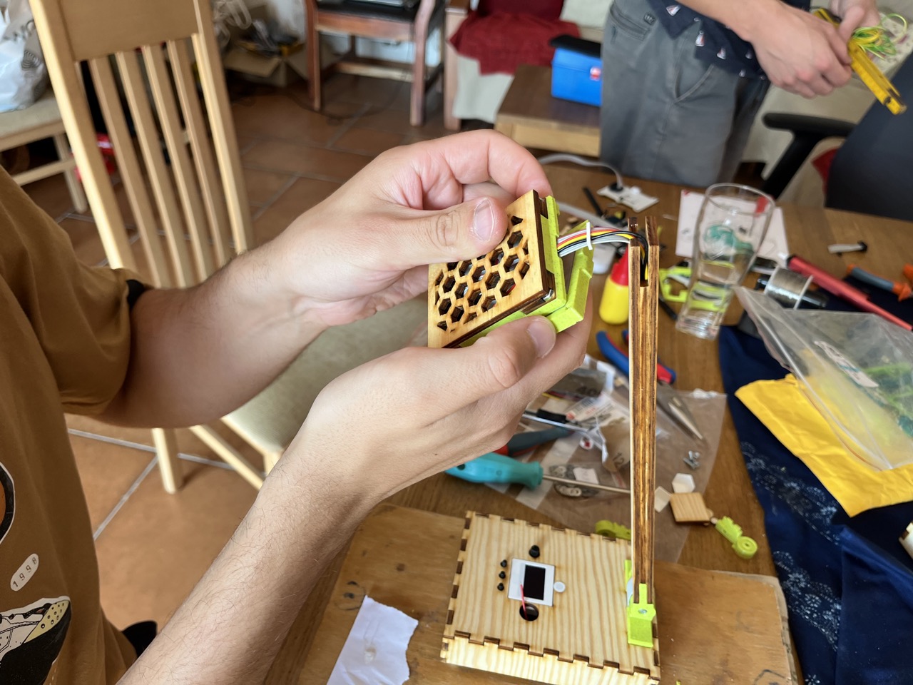
Manuals/SupportFiles/IMG_5134.jpeg
