Vedatori/PaLampa/Manuals/SupportFiles/IMG_5137.jpeg

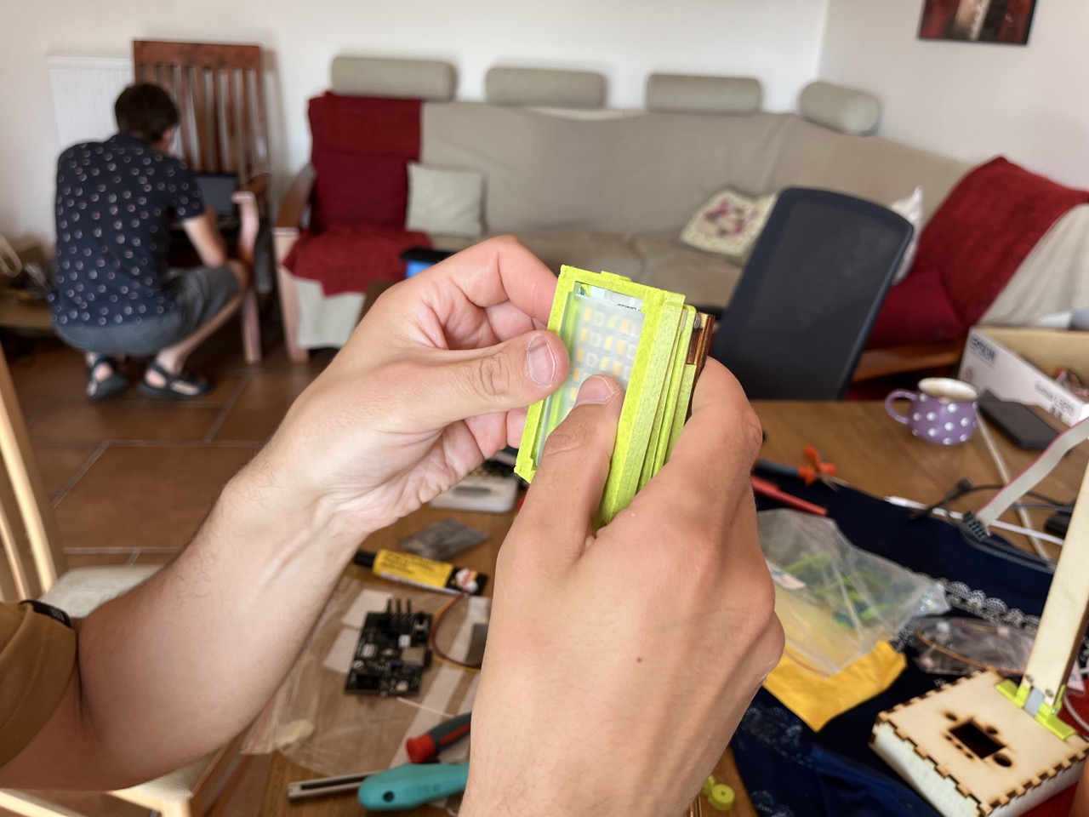
Manuals/SupportFiles/IMG_5137.jpeg
