Vedatori/PaLampa/Manuals/SupportFiles/IMG_5138.jpeg

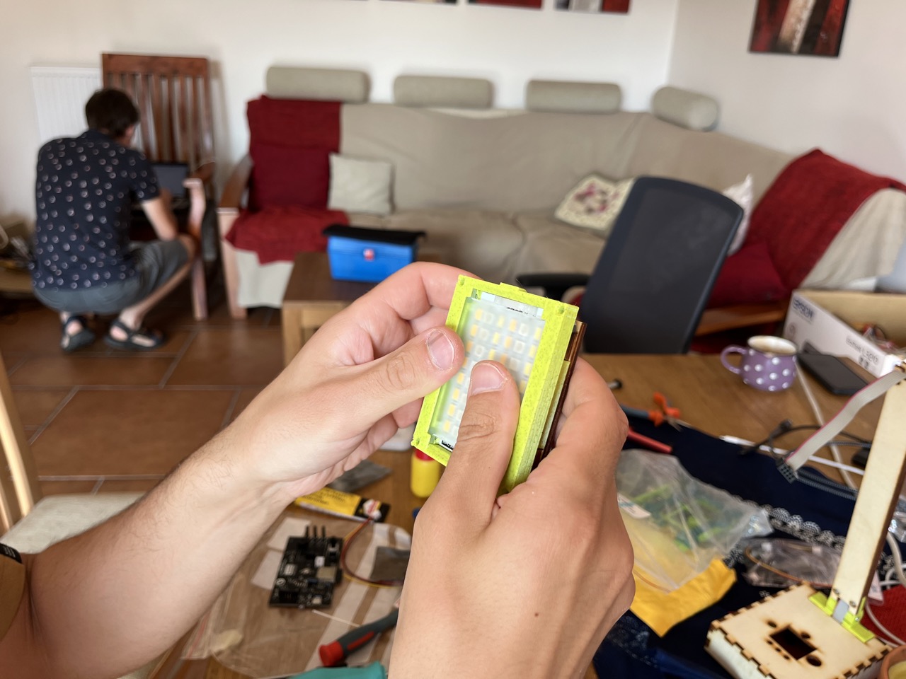
Manuals/SupportFiles/IMG_5138.jpeg
