Vedatori/PaLampa/Manuals/SupportFiles/IMG_5141.jpeg

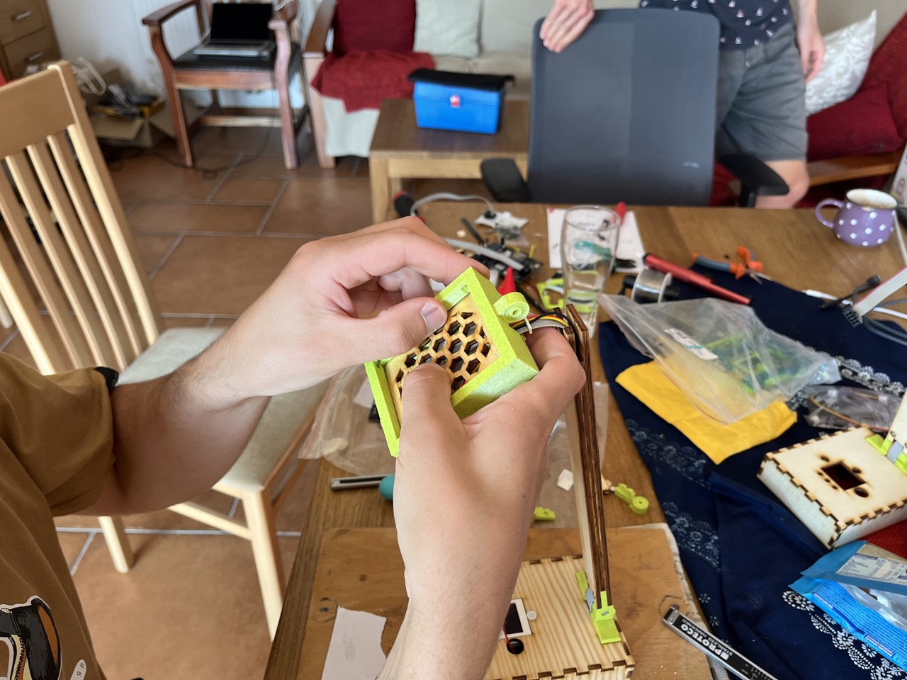
Manuals/SupportFiles/IMG_5141.jpeg
