Vedatori/PaLampa/Manuals/SupportFiles/IMG_5142.jpeg

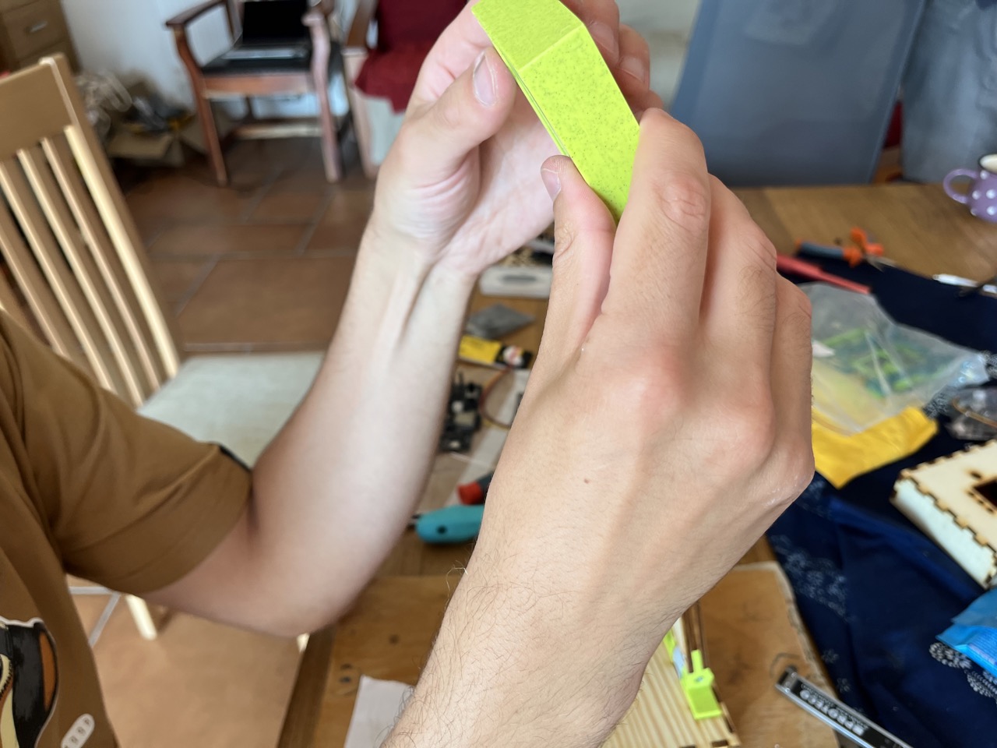
Manuals/SupportFiles/IMG_5142.jpeg
