Vedatori/PaLampa/Manuals/SupportFiles/IMG_5143.jpeg

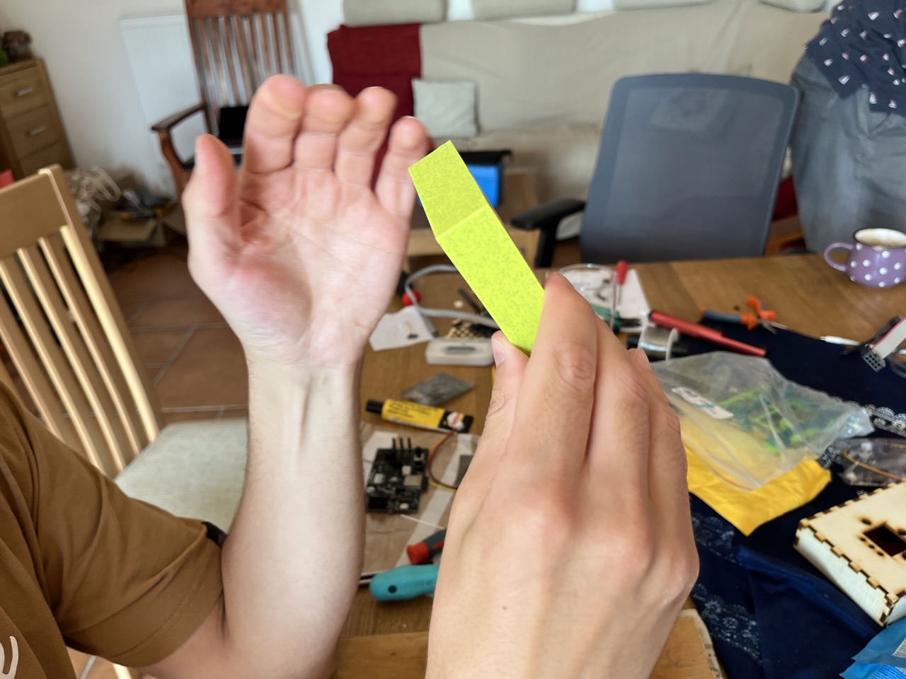
Manuals/SupportFiles/IMG_5143.jpeg
