Vedatori/PaLampa/Manuals/SupportFiles/IMG_5144.jpeg

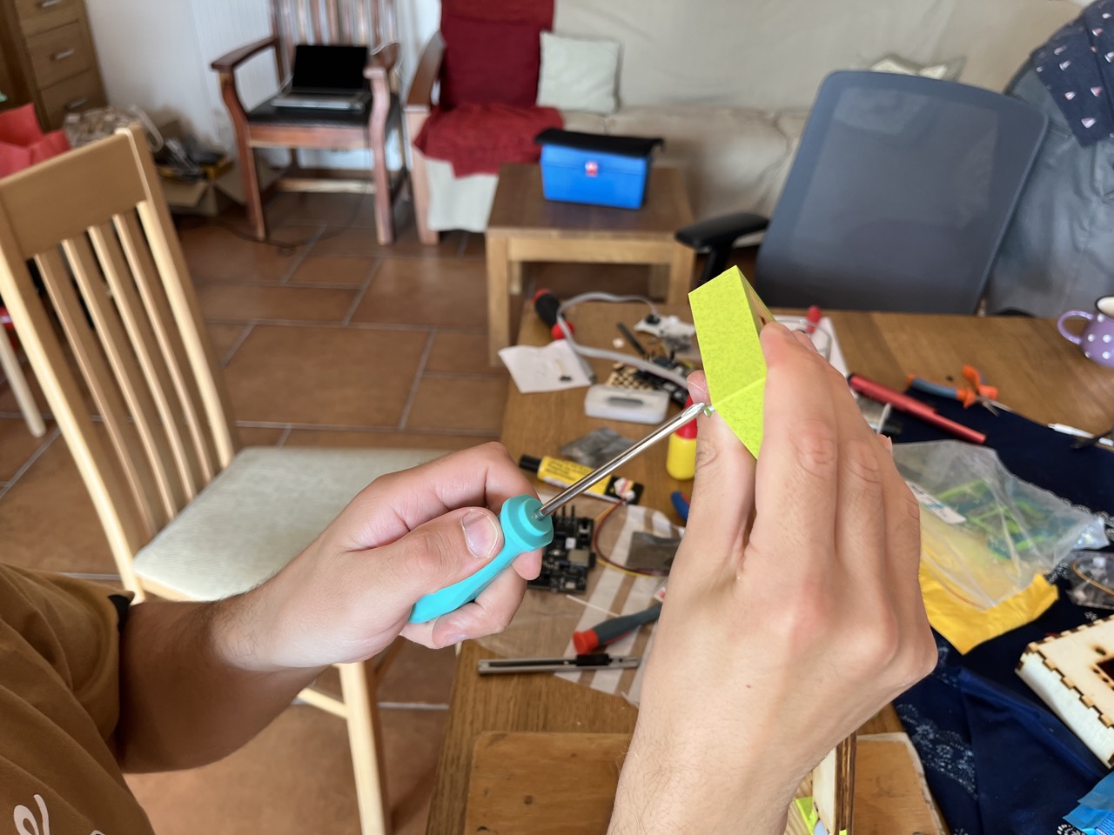
Manuals/SupportFiles/IMG_5144.jpeg
