Vedatori/PaLampa/Manuals/SupportFiles/IMG_5146.jpeg

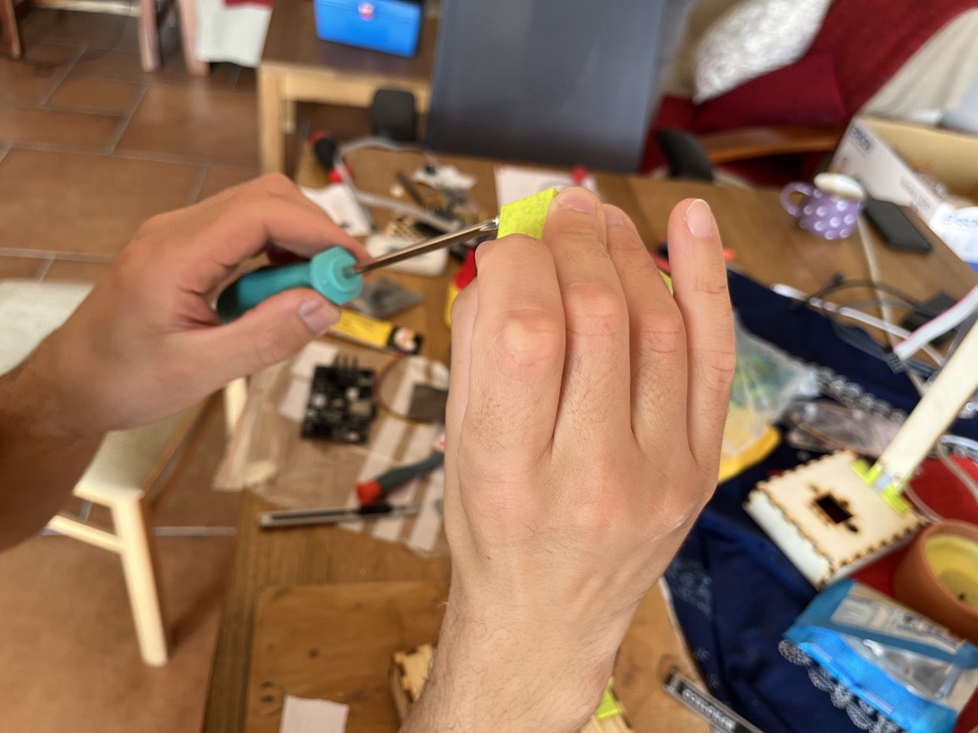
Manuals/SupportFiles/IMG_5146.jpeg
