Vedatori/PaLampa/Manuals/SupportFiles/IMG_5148.jpeg

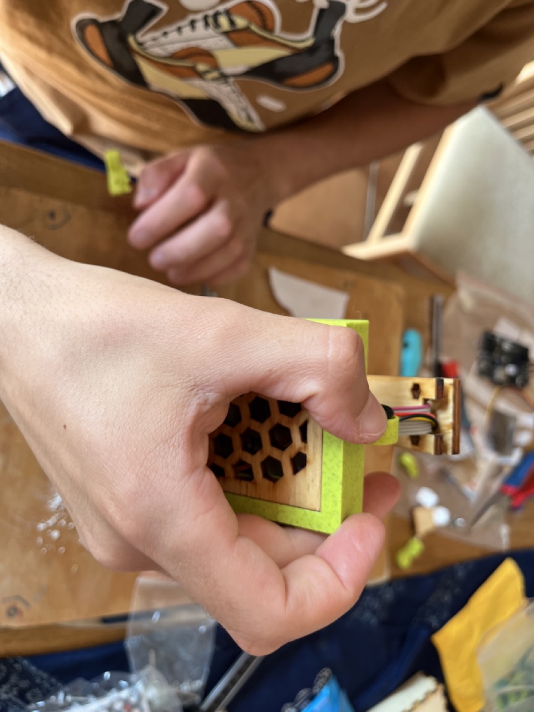
Manuals/SupportFiles/IMG_5148.jpeg
