Vedatori/PaLampa/Manuals/SupportFiles/IMG_5149.jpeg

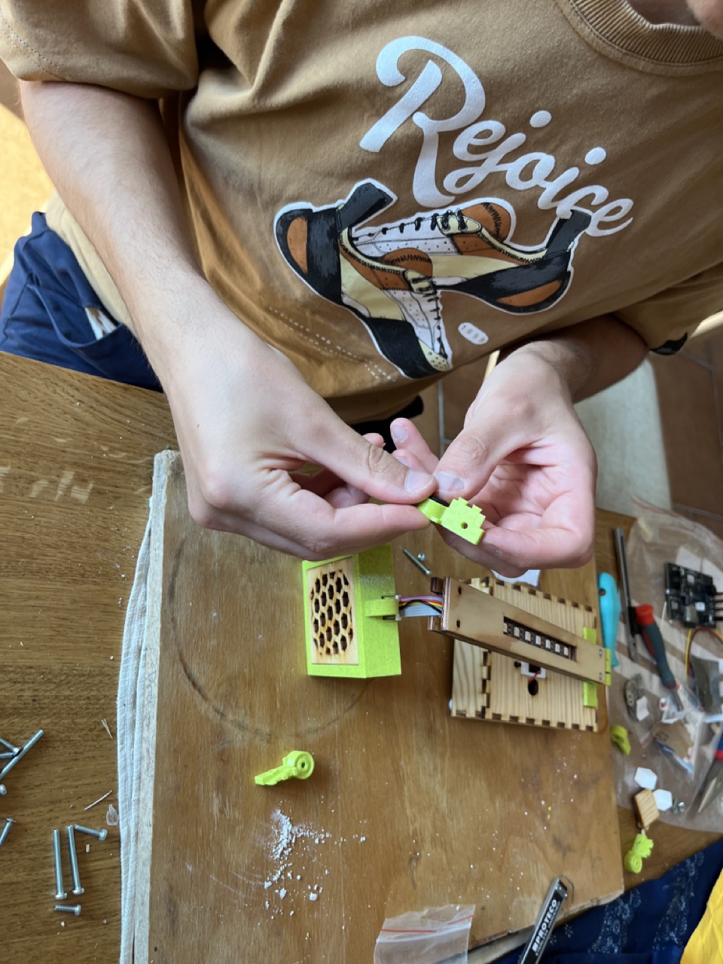
Manuals/SupportFiles/IMG_5149.jpeg
