Vedatori/PaLampa/Manuals/SupportFiles/IMG_5150.jpeg

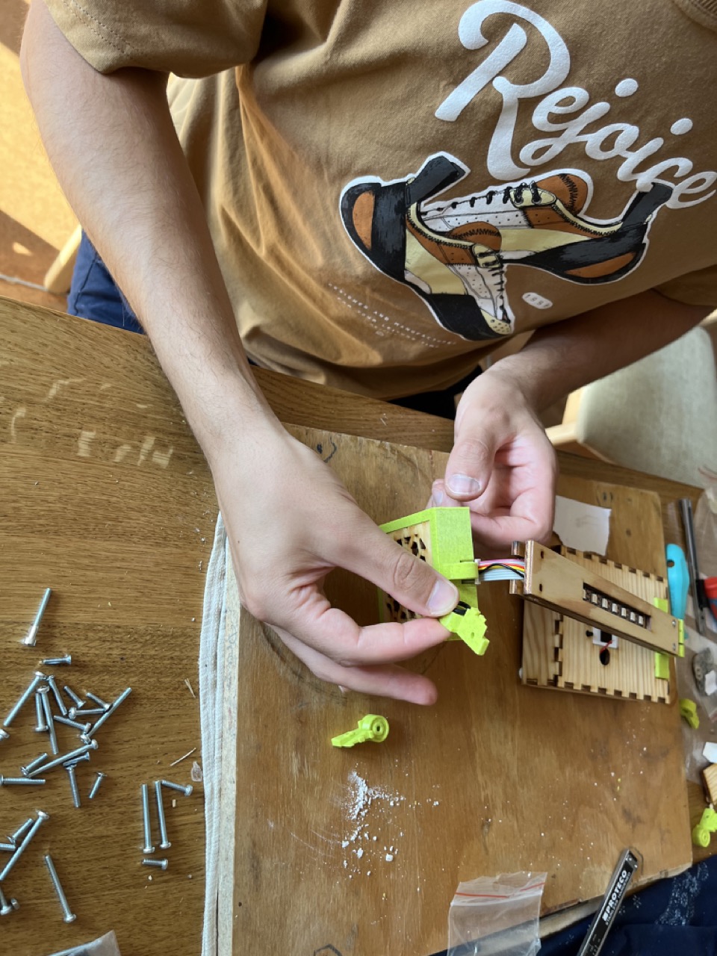
Manuals/SupportFiles/IMG_5150.jpeg
