Vedatori/PaLampa/Manuals/SupportFiles/IMG_5152.jpeg

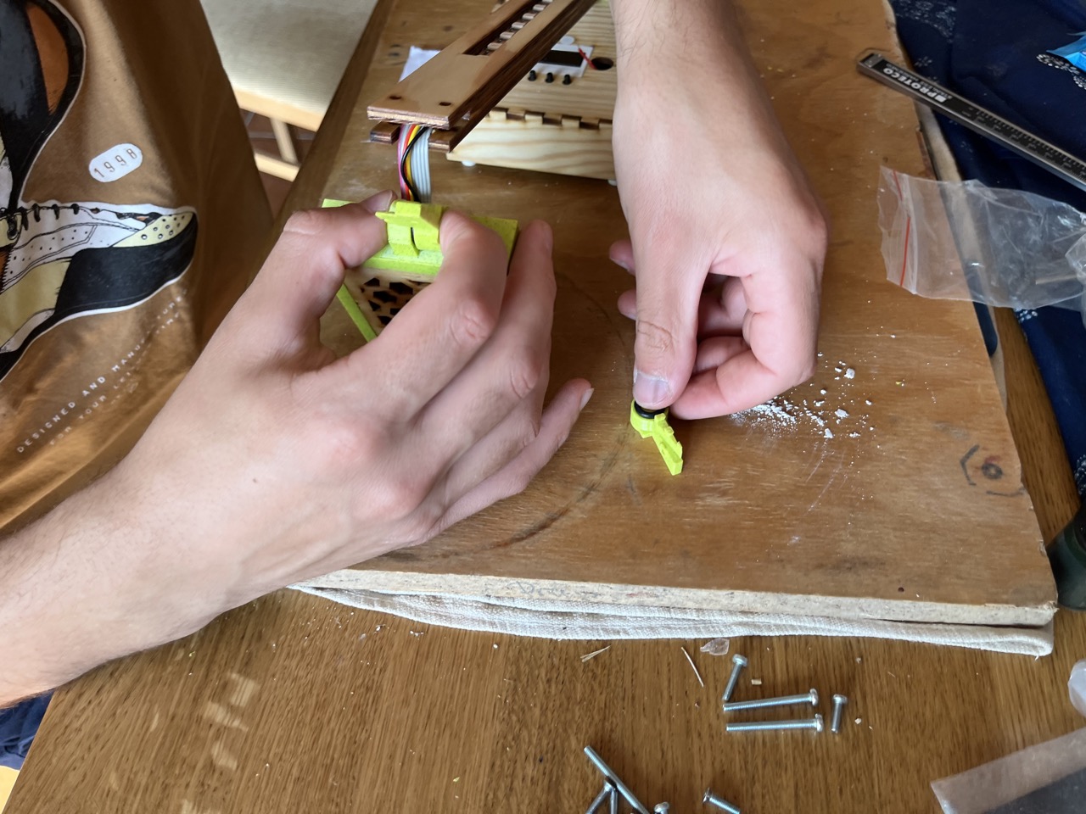
Manuals/SupportFiles/IMG_5152.jpeg
