Vedatori/PaLampa/Manuals/SupportFiles/IMG_5153.jpeg

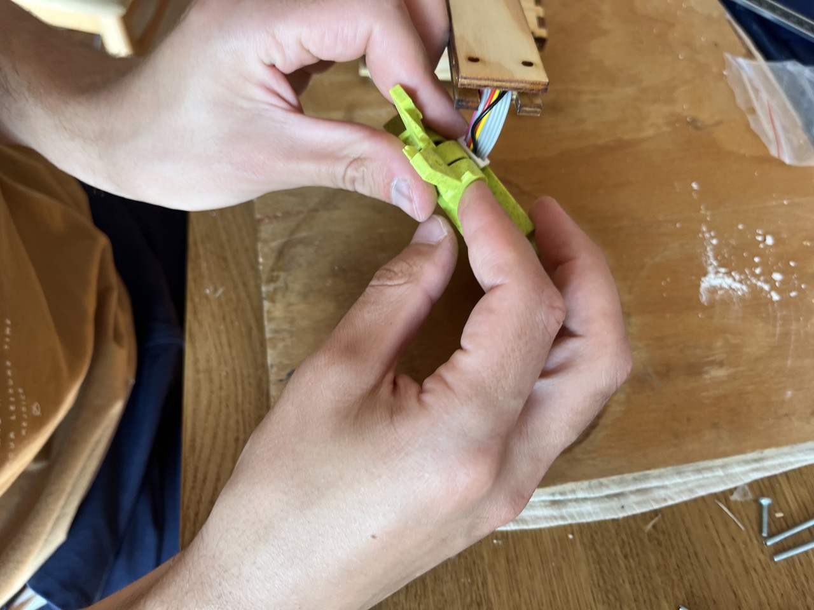
Manuals/SupportFiles/IMG_5153.jpeg
