Vedatori/PaLampa/Manuals/SupportFiles/IMG_5169.jpeg

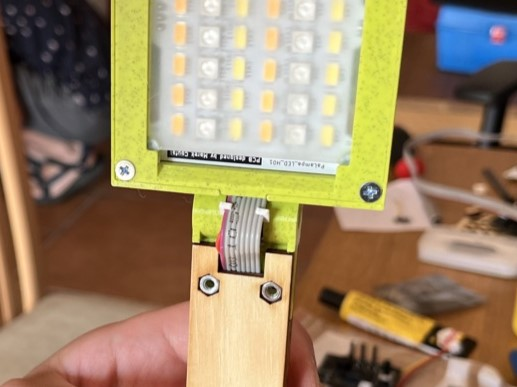
Manuals/SupportFiles/IMG_5169.jpeg
