Vedatori/PaLampa/Manuals/SupportFiles/IMG_5646-min.jpg

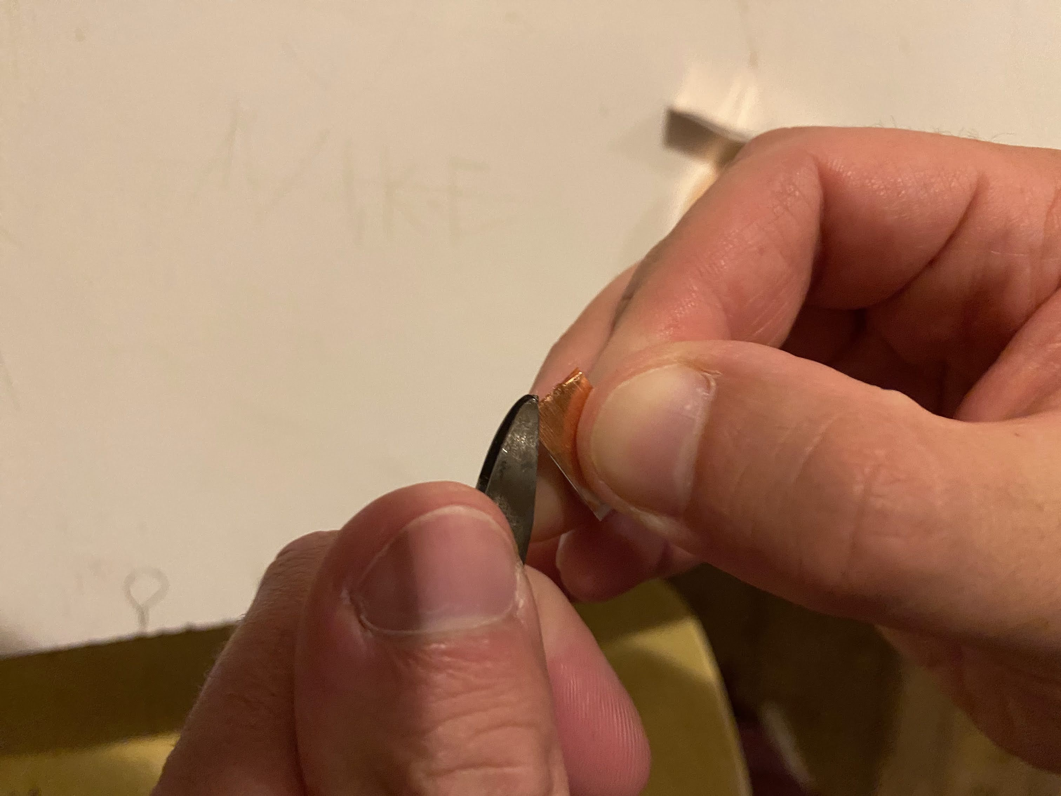
Manuals/SupportFiles/IMG_5646-min.jpg
