Vedatori/PaLampa/Manuals/SupportFiles/prog_hint.jpeg

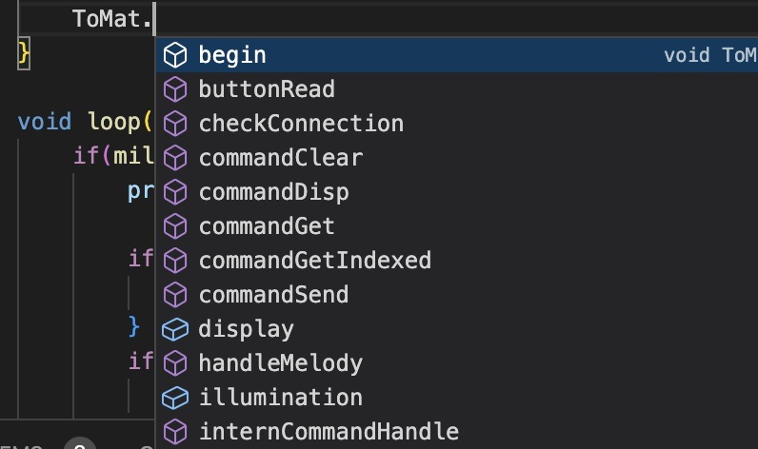
Manuals/SupportFiles/prog_hint.jpeg
