Vedatori/PaLampa/Manuals/SupportFiles/prog_web_root.jpeg

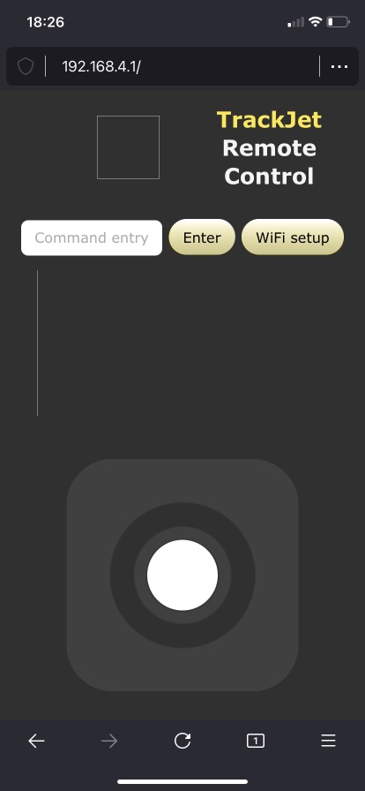
Manuals/SupportFiles/prog_web_root.jpeg
