Vedatori/PaLampa/Software/demo_project/src/PaLampa/Oled_module.h

#pragma once

#include <Adafruit_SSD1306.h>

class Oled_module
{
private:
    Adafruit_SSD1306 display;
    int SCREEN_ADDRESS;
    int SCREEN_WIDTH;
    int SCREEN_HEIGHT;
public:

    /// @brief Constructor
    /// @param ADDRESS I2C address
    Oled_module(int SCREEN_WIDTH, int SCREEN_HEIGHT, int ADDRESS);

    /// @brief Must be called before using any other functions
    void begin();

    /// @brief Enables/disables the automatic sendClear task
    bool autoSend = true;

    bool dataChanged = false;
    
    bool widgetMap[2][8];
    void widgetMapClear();
    bool widgetMapFindSpot(int& w, int& h, bool reserve = true);
    void widgetMapPrint();
    void widgetMapReserve(int c0, int c1, int r0, int r1);

    /// @brief Returns the internal adafruit gfx object for direct access to the display
    Adafruit_SSD1306& getDisplay() { return display; }

    /// @brief Sends buffer and clears it
    /// @param autoSendTask If this function is used by a background task (not the user), set this to true.
    void sendClear(bool autoSendTask = false);

    /// @brief Shows the "Vědátoři" logo on the display
    void drawLogo();

    // =========================== Widgets
    /*
    Display is divided into 2 columns and 8 rows
    */

    /// (WIP)
    /// @brief Displays a clock (11:40)
    /// @param size The size of text (1 - 4), 1 & 2 is single column, 3 & 4 is double column
    void widgetText(String text ,int16_t size, int column = -1, int row = -1);
    

    
};

namespace oled_module {

const unsigned char vedatoriBitmap128x64 [] PROGMEM =
{
    // 'vedatori_black', 128x64px
    0x00, 0x00, 0x00, 0x00, 0x00, 0x00, 0x00, 0x00, 0x00, 0x00, 0x00, 0x00, 0x00, 0x00, 0x00, 0x00, 
    0x00, 0x00, 0x00, 0x00, 0x00, 0x00, 0x00, 0x00, 0x00, 0x00, 0x00, 0x00, 0x00, 0x00, 0x00, 0x00, 
    0x00, 0x00, 0x00, 0x00, 0x00, 0x00, 0x00, 0x00, 0x00, 0x00, 0x00, 0x00, 0x00, 0x00, 0x00, 0x00, 
    0x00, 0x00, 0x00, 0x00, 0x00, 0x00, 0x00, 0x00, 0x00, 0x00, 0x00, 0x00, 0x00, 0x00, 0x00, 0x00, 
    0x00, 0x00, 0x00, 0x00, 0x00, 0x00, 0x00, 0x00, 0x00, 0x00, 0x00, 0x00, 0x00, 0x00, 0x00, 0x00, 
    0x00, 0x00, 0x00, 0x00, 0x00, 0x00, 0x00, 0x00, 0x00, 0x00, 0x00, 0x00, 0x00, 0x00, 0x00, 0x00, 
    0x00, 0x00, 0x00, 0x00, 0x00, 0x00, 0x00, 0x00, 0x00, 0x00, 0x00, 0x00, 0x00, 0x00, 0x00, 0x00, 
    0x00, 0x00, 0x00, 0x00, 0x00, 0x00, 0x00, 0x00, 0x00, 0x00, 0x00, 0x00, 0x00, 0x00, 0x00, 0x00, 
    0x00, 0x00, 0x00, 0x00, 0x00, 0x00, 0x00, 0x00, 0x00, 0x00, 0x00, 0x00, 0x00, 0x00, 0x00, 0x00, 
    0x00, 0x00, 0x00, 0x00, 0x00, 0x00, 0x00, 0x00, 0x00, 0x00, 0x00, 0x00, 0x00, 0x00, 0x00, 0x00, 
    0x00, 0x00, 0x00, 0x00, 0x00, 0x00, 0x00, 0x00, 0x00, 0x00, 0x00, 0x00, 0x00, 0x00, 0x00, 0x00, 
    0x00, 0x00, 0x00, 0x00, 0x00, 0x00, 0x00, 0x00, 0x00, 0x00, 0x00, 0x00, 0x00, 0x00, 0x00, 0x00, 
    0x00, 0x00, 0x00, 0x00, 0x00, 0x00, 0x00, 0x00, 0x00, 0x00, 0x00, 0x00, 0x00, 0x00, 0x00, 0x00, 
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
    0x0f, 0xff, 0x00, 0x00, 0x00, 0x00, 0x00, 0x00, 0x00, 0x00, 0x00, 0x00, 0x00, 0x00, 0x00, 0x00, 
    0x02, 0xaa, 0x00, 0x00, 0x00, 0x00, 0x00, 0x00, 0x00, 0x00, 0x00, 0x00, 0x00, 0x00, 0x00, 0x00, 
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
};

}
