Vedatori/PaLampa/Software/demo_project/src/PaLampa/WiFiCaptain.h

#ifndef _WIFI_CAPTAIN_
#define _WIFI_CAPTAIN_

#include "Arduino.h"
#include "WebSocketsServer.h"   //https://github.com/Links2004/arduinoWebSockets
#include <WebServer.h>
#include <Update.h>

struct credentials {
    char ssid[33] = "";
    char password[65] = "";
};

extern WebServer webserver;

void handleRoot();
void handleStatus();
void handleStyle();
void handleRedirectRoot();
void redirect(String path);
void handleSoftApEnable();
void handleWifi();
void handleWifiSave();
void handleOtaUpload();
void handleOtaUploadProgress();
void handleOtaUpdate();
void handleNotFound();
void softApEnable();
void softApDisable();
void connectWifiAsClient(const credentials aCredentials);
void loadCredentials();
void saveCredentials(const credentials aCredentials);
void wifiCaptInit();
void handleClients(void * param);
bool getLastConnectionType();
void setApCredentials(String ssid, String password);
String ipToDisp();

void onWebSocketEvent(uint8_t client_num, WStype_t type, uint8_t * payload, size_t length);
char * commandGetCaptain();
void commandClearCaptain();
void commandSendCaptain(String msgType, String payload);

#endif // _WIFI_CAPTAIN_
